oomlout/oomlout_oobb_part_holder_bearing_version_5/navigation_oobb/oobb/part/plate/bearing/6705_bearing_size/3_width/3_height/12_depth/motor_servo_standard_01_horn_adapter_screws/3dpr.png

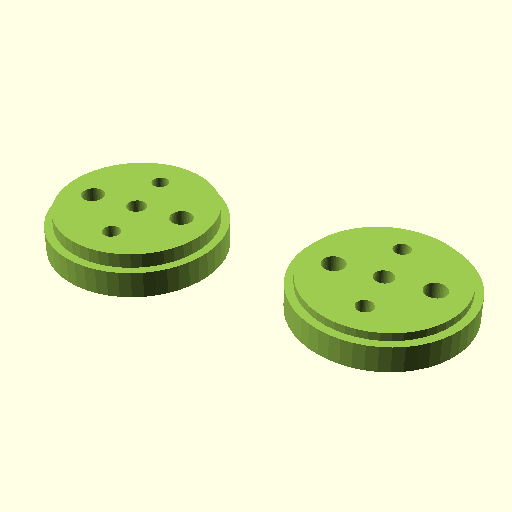
navigation_oobb/oobb/part/plate/bearing/6705_bearing_size/3_width/3_height/12_depth/motor_servo_standard_01_horn_adapter_screws/3dpr.png
