oomlout/oomlout_oobb_part_holder_bearing_version_5/navigation_oobb/oobb/part/plate/bearing/6709_bearing_size/5_width/5_height/12_depth/inside_embedded_m3_nuts/3dpr.png

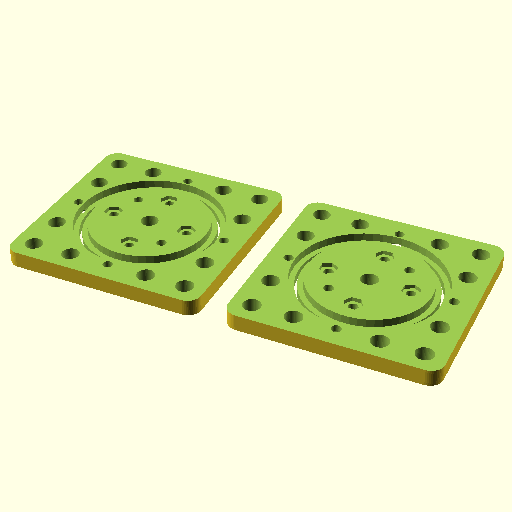
navigation_oobb/oobb/part/plate/bearing/6709_bearing_size/5_width/5_height/12_depth/inside_embedded_m3_nuts/3dpr.png
