oomlout/oomlout_oobb_part_holder_bearing_version_5/navigation_oobb/oobb/part/plate/bearing/6709_bearing_size/5_width/5_height/12_depth/motor_building_block_large_01/3dpr.stl

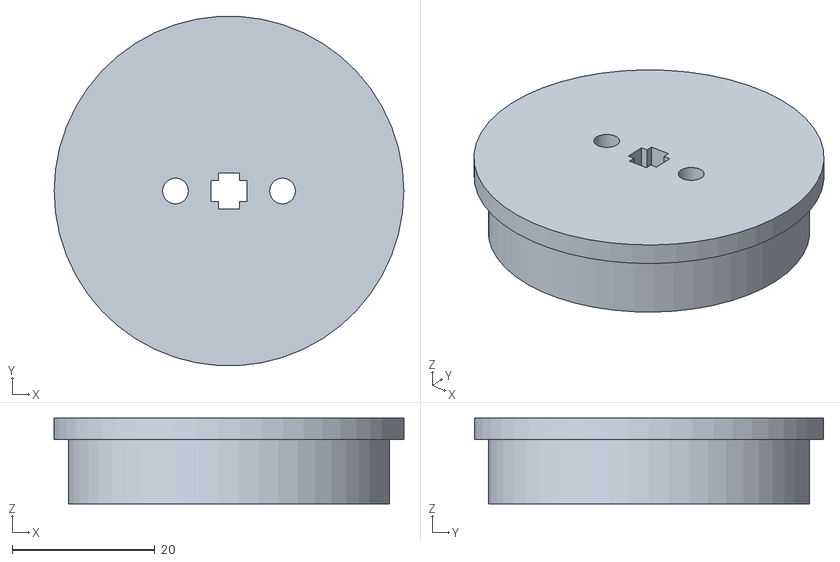
[picture p25: CAD file, 2026-10-08]
navigation_oobb/oobb/part/plate/bearing/6709_bearing_size/5_width/5_height/12_depth/motor_building_block_large_01/3dpr.stl
49.0 x 48.9 x 12.0
