oomlout/oomlout_oobb_part_holder_bearing_version_5/navigation_oobb/oobb/part/plate/bearing/6709_bearing_size/5_width/5_height/12_depth/motor_n20/3dpr.stl

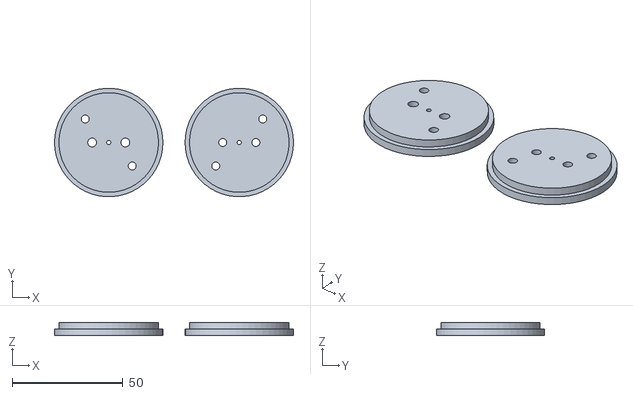
[picture p26: CAD file, 2026-10-08]
navigation_oobb/oobb/part/plate/bearing/6709_bearing_size/5_width/5_height/12_depth/motor_n20/3dpr.stl
108.0 x 48.9 x 6.00
