oomlout/oomlout_oobb_part_holder_bearing_version_5/navigation_oobb/oobb/part/plate/bearing/6709_bearing_size/5_width/5_height/12_depth/motor_servo_micro_01/true.stl

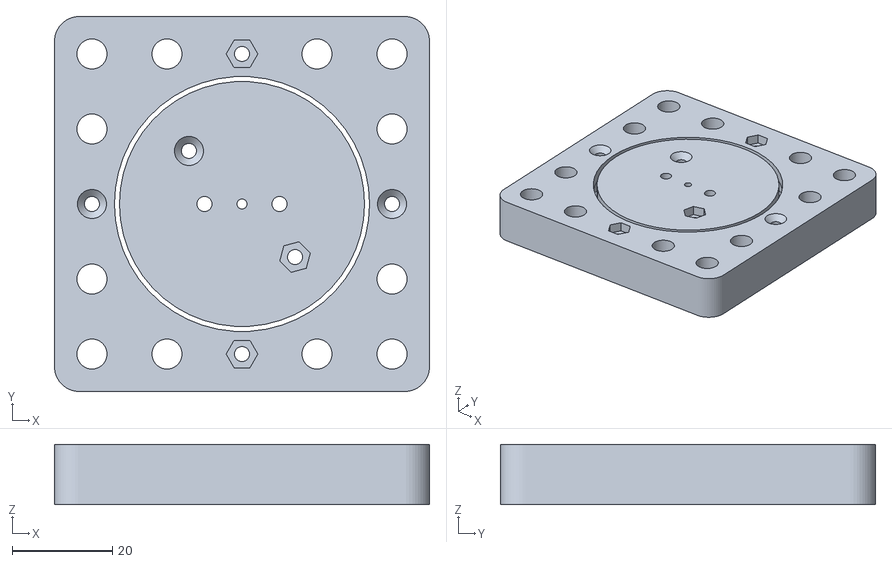
[picture p27: CAD file, 2026-10-08]
navigation_oobb/oobb/part/plate/bearing/6709_bearing_size/5_width/5_height/12_depth/motor_servo_micro_01/true.stl
75.0 x 75.0 x 12.0
