oomlout/oomlout_oobb_part_holder_bearing_version_5/navigation_oobb/oobb/part/plate/bearing/6803_bearing_size/3_width/3_height/12_depth/laser.stl

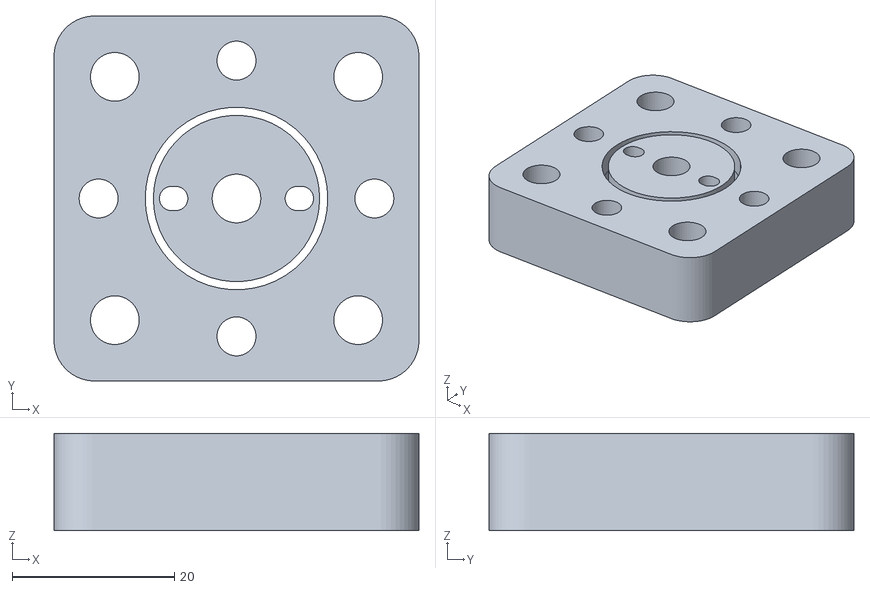
[picture p28: CAD file, 2026-10-08]
navigation_oobb/oobb/part/plate/bearing/6803_bearing_size/3_width/3_height/12_depth/laser.stl
45.0 x 45.0 x 12.0
