oomlout/oomlout_oobb_part_holder_bearing_version_5/navigation_oobb/oobb/part/plate/bearing/6810_bearing_size/7_width/5_height/12_depth/inside_embedded_m3_nuts/true.stl

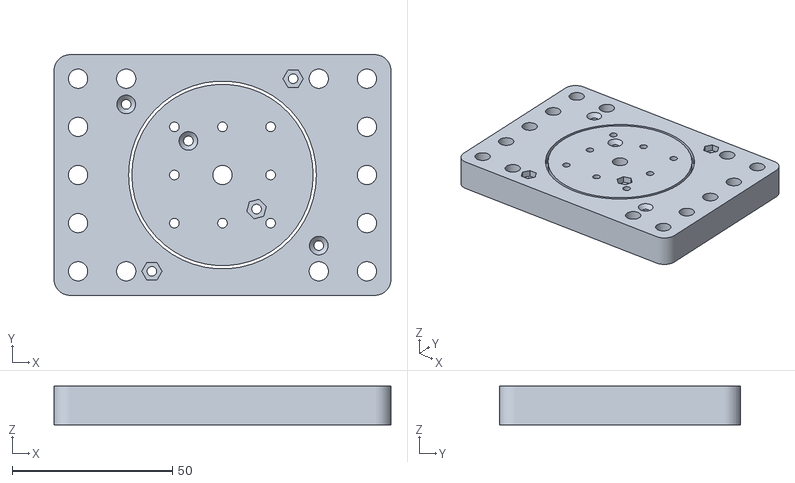
[picture p30: CAD file, 2026-10-08]
navigation_oobb/oobb/part/plate/bearing/6810_bearing_size/7_width/5_height/12_depth/inside_embedded_m3_nuts/true.stl
105.0 x 75.0 x 12.0
