oomlout/oomlout_oobb_part_holder_bearing_version_5/navigation_oobb/oobb/part/plate_90_degree/bearing/606_bearing_size/3_width/3_height/12_depth/3dpr.stl

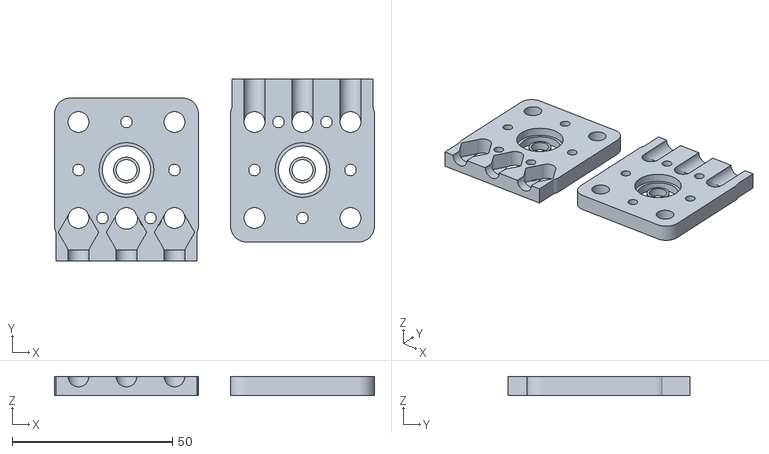
[picture p31: CAD file, 2026-10-08]
navigation_oobb/oobb/part/plate_90_degree/bearing/606_bearing_size/3_width/3_height/12_depth/3dpr.stl
100.0 x 57.0 x 6.00
