oomlout/oomlout_oobb_part_holder_bearing_version_5/navigation_oobb/oobb/part/plate_90_degree/bearing/606_bearing_size/3_width/3_height/12_depth/basic/laser.stl

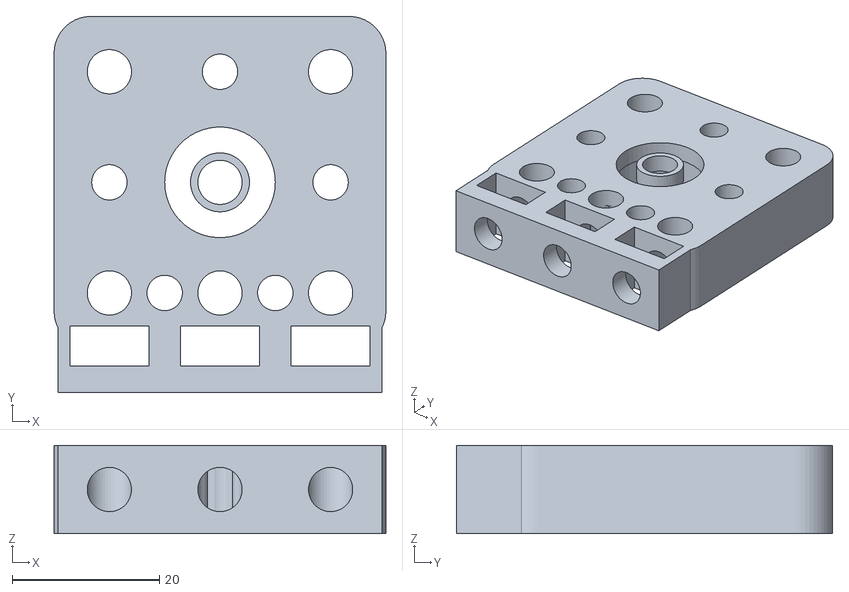
[picture p32: CAD file, 2026-10-08]
navigation_oobb/oobb/part/plate_90_degree/bearing/606_bearing_size/3_width/3_height/12_depth/basic/laser.stl
45.0 x 51.0 x 12.0
