oomlout/oomlout_oobb_part_holder_bearing_version_5/parts/oobb_part_plate_90_degree_bearing_606_bearing_size_3_width_3_height_12_depth_basic/true.stl

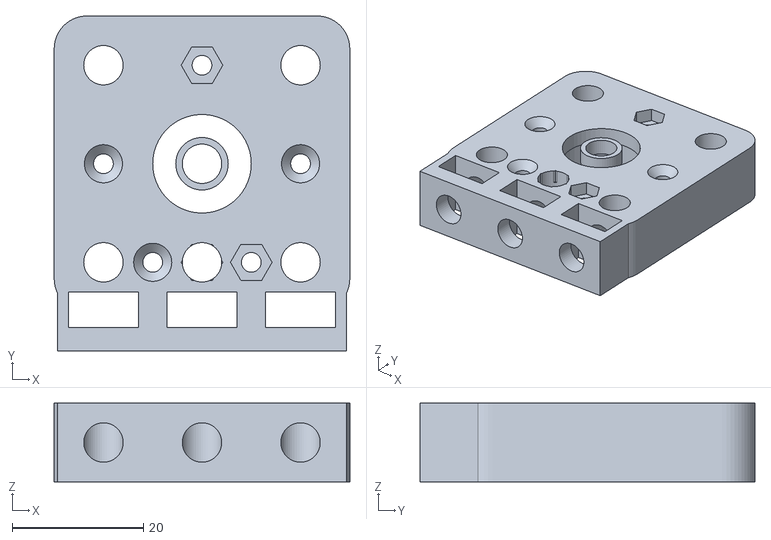
[picture p33: CAD file, 2026-10-08]
parts/oobb_part_plate_90_degree_bearing_606_bearing_size_3_width_3_height_12_depth_basic/true.stl
45.0 x 51.0 x 12.0
