oomlout/oomlout_oobb_part_holder_bearing_version_5/parts/oobb_part_plate_bearing_606_bearing_size_3_width_3_height_12_depth/3dpr.stl

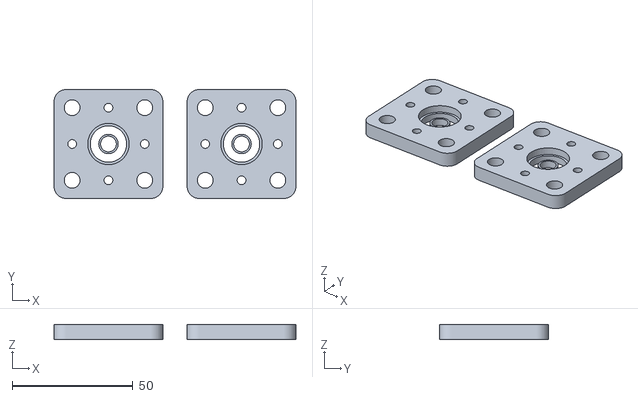
[picture p34: CAD file, 2026-10-08]
parts/oobb_part_plate_bearing_606_bearing_size_3_width_3_height_12_depth/3dpr.stl
100.0 x 45.0 x 6.00
