oomlout/oomlout_oobb_part_holder_bearing_version_5/parts/oobb_part_plate_bearing_6704_bearing_size_3_width_3_height_12_depth_motor_gearmotor_01/true.stl

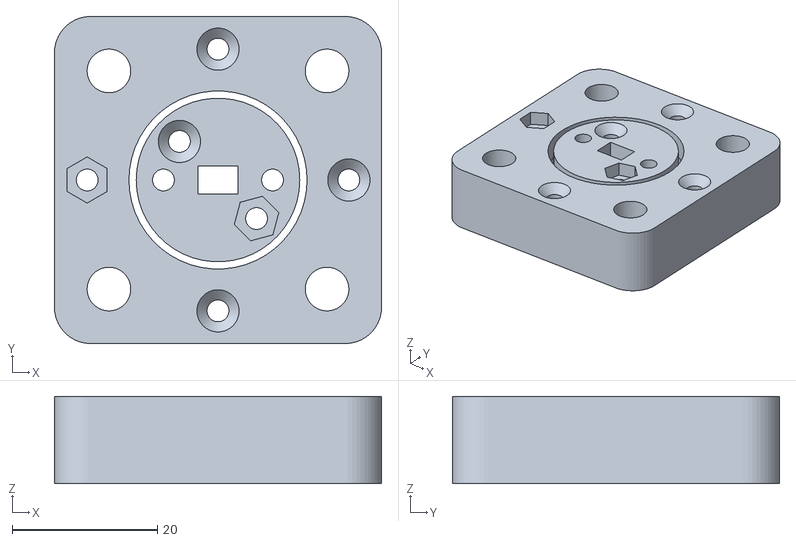
[picture p37: CAD file, 2026-10-08]
parts/oobb_part_plate_bearing_6704_bearing_size_3_width_3_height_12_depth_motor_gearmotor_01/true.stl
45.0 x 45.0 x 12.0
