oomlout/oomlout_oobb_part_holder_bearing_version_5/parts/oobb_part_plate_bearing_6704_bearing_size_3_width_3_height_12_depth_motor_n20/3dpr.stl

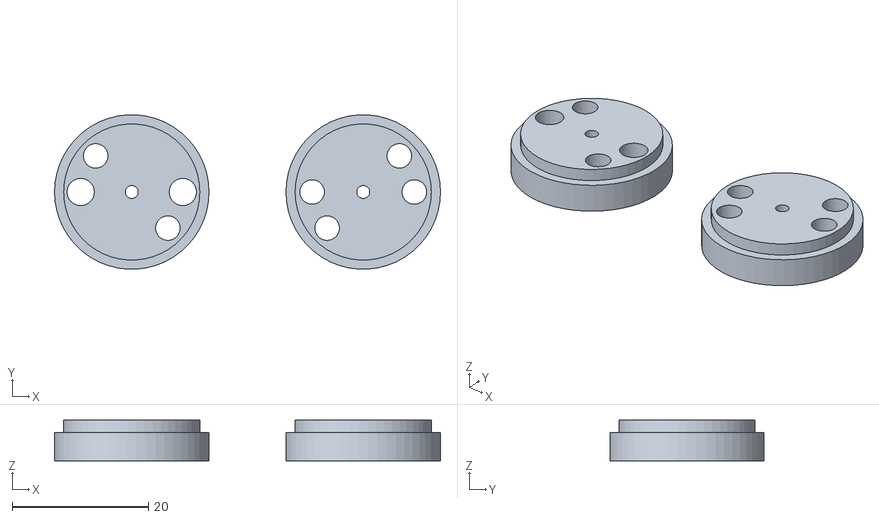
[picture p38: CAD file, 2026-10-08]
parts/oobb_part_plate_bearing_6704_bearing_size_3_width_3_height_12_depth_motor_n20/3dpr.stl
56.7 x 22.7 x 6.00
