oomlout/oomlout_oobb_part_holder_bearing_version_5/parts/oobb_part_plate_bearing_6705_bearing_size_3_width_3_height_12_depth_motor_n20/true.stl

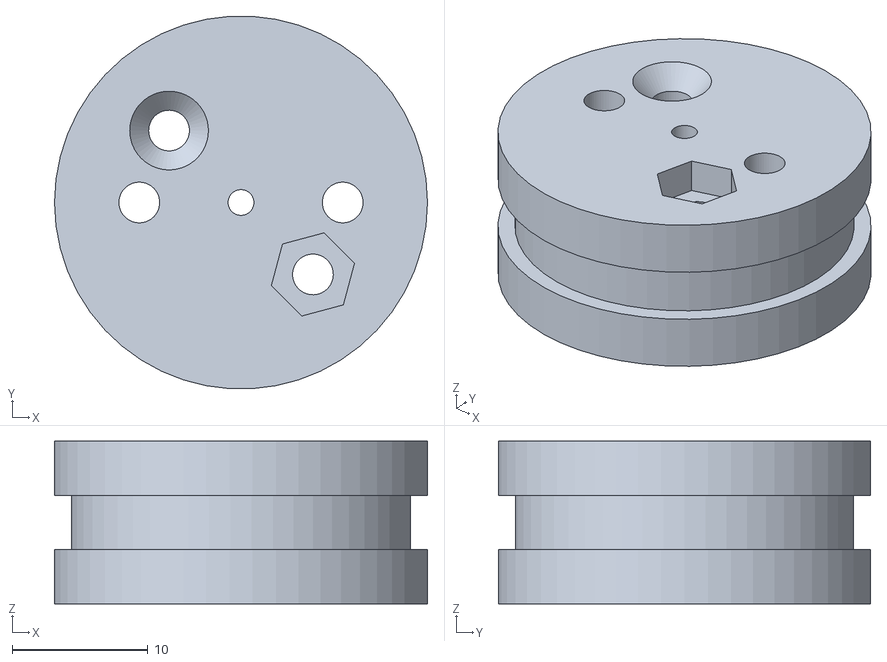
[picture p39: CAD file, 2026-10-08]
parts/oobb_part_plate_bearing_6705_bearing_size_3_width_3_height_12_depth_motor_n20/true.stl
27.5 x 27.4 x 12.0
