oomlout/oomlout_oobb_part_holder_bearing_version_5/parts/oobb_part_plate_bearing_6709_bearing_size_5_width_5_height_12_depth_inside_embedded_m6_nuts/laser.stl

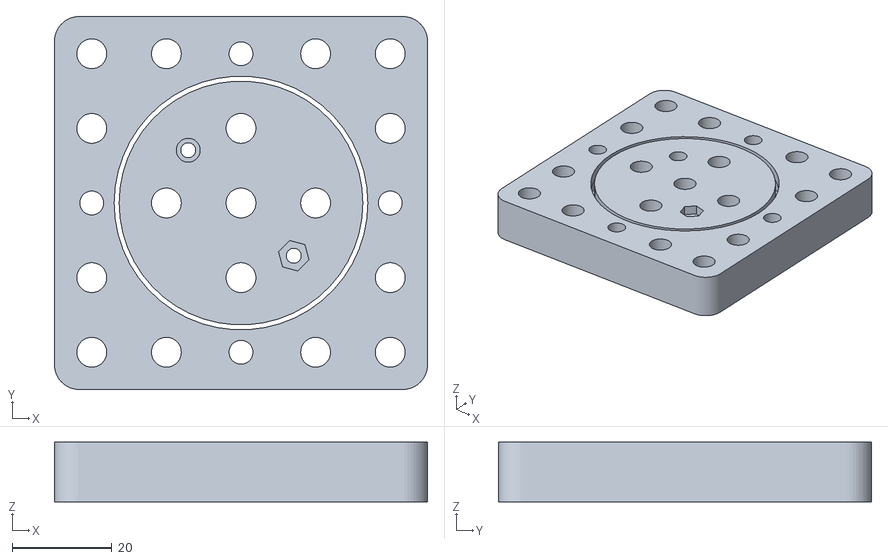
[picture p40: CAD file, 2026-10-08]
parts/oobb_part_plate_bearing_6709_bearing_size_5_width_5_height_12_depth_inside_embedded_m6_nuts/laser.stl
75.0 x 75.0 x 12.0
