oomlout/oomlout_oobb_part_holder_bearing_version_5/parts/oobb_part_plate_bearing_6709_bearing_size_5_width_5_height_12_depth_motor_building_block_large_01/laser.stl

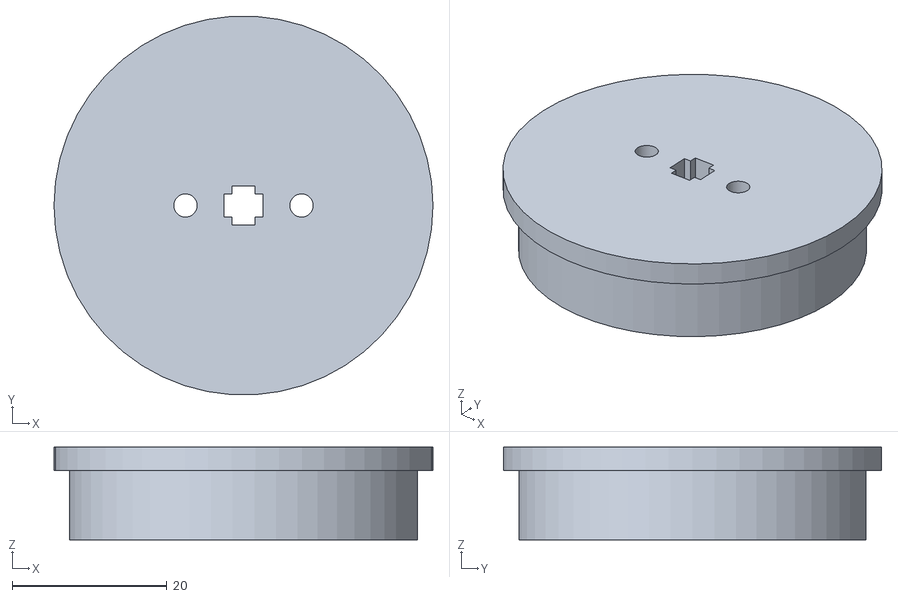
[picture p41: CAD file, 2026-10-08]
parts/oobb_part_plate_bearing_6709_bearing_size_5_width_5_height_12_depth_motor_building_block_large_01/laser.stl
49.0 x 48.9 x 12.0
