oomlout/oomlout_oobb_part_holder_bearing_version_5/parts/oobb_part_plate_bearing_6810_bearing_size_7_width_5_height_12_depth/laser.stl

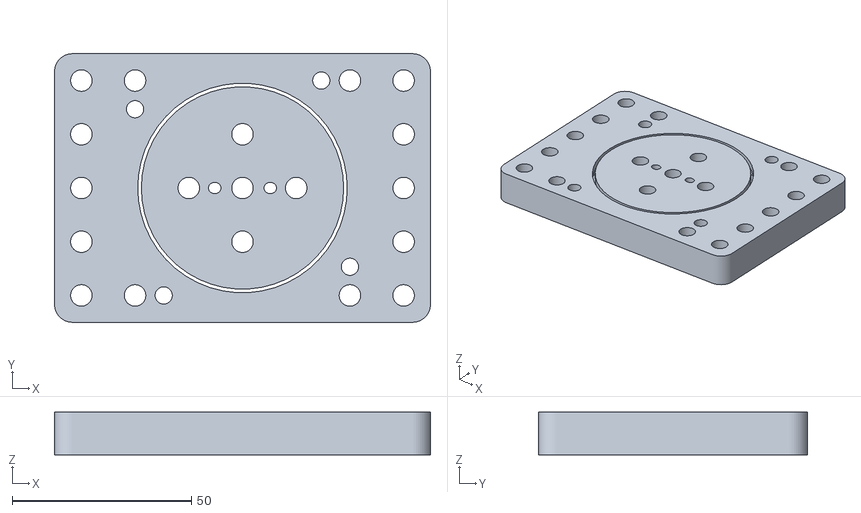
[picture p43: CAD file, 2026-10-08]
parts/oobb_part_plate_bearing_6810_bearing_size_7_width_5_height_12_depth/laser.stl
105.0 x 75.0 x 12.0
