oomlout/oomlout_oobb_part_holder_bearing_version_5/navigation_oobb/oobb/part/plate/bearing/606_bearing_size/3_width/3_height/12_depth/true.stl

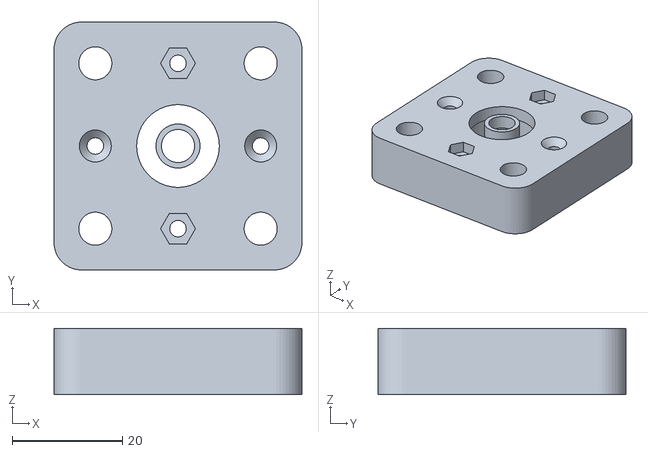
[picture p44: CAD file, 2026-10-08]
navigation_oobb/oobb/part/plate/bearing/606_bearing_size/3_width/3_height/12_depth/true.stl
45.0 x 45.0 x 12.0
