oomlout/oomlout_oobb_part_holder_bearing_version_5/navigation_oobb/oobb/part/plate/bearing/6810_bearing_size/7_width/5_height/12_depth/inside_embedded_m3_nuts/3dpr.stl

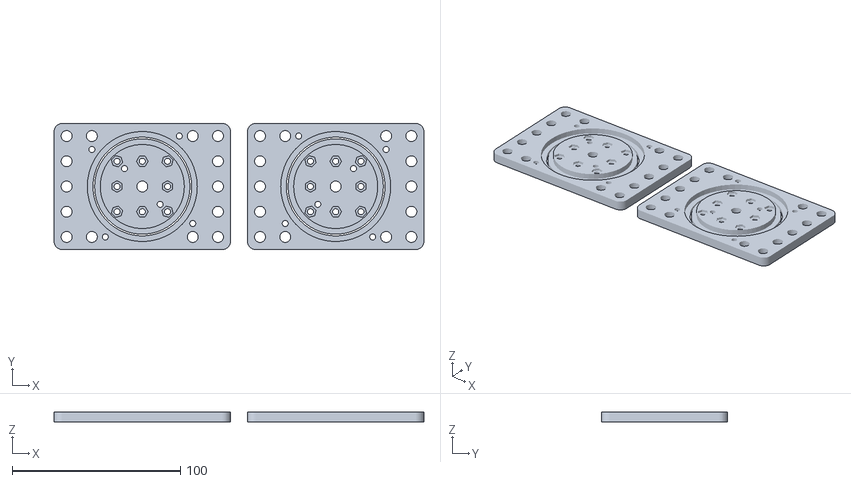
[picture p46: CAD file, 2026-10-08]
navigation_oobb/oobb/part/plate/bearing/6810_bearing_size/7_width/5_height/12_depth/inside_embedded_m3_nuts/3dpr.stl
220.0 x 75.0 x 6.00
