oomlout/oomlout_oobb_part_holder_bearing_version_5/parts/oobb_part_plate_bearing_608_bearing_size_3_width_3_height_12_depth/laser.stl

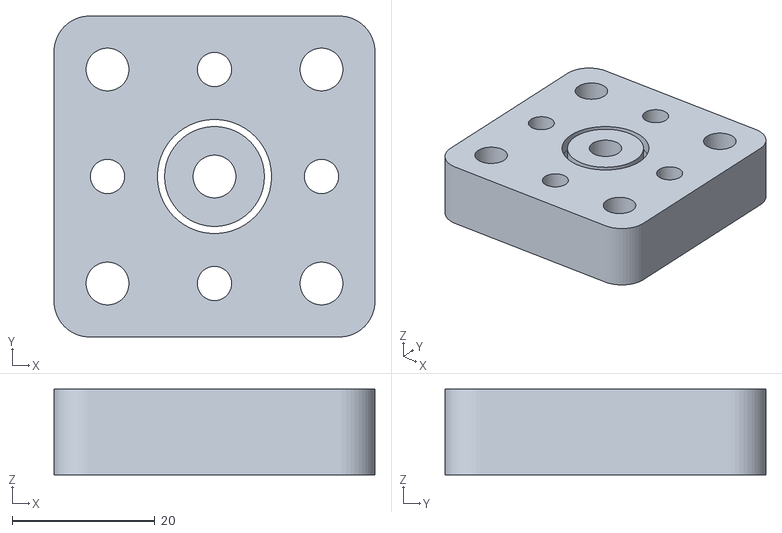
[picture p47: CAD file, 2026-10-08]
parts/oobb_part_plate_bearing_608_bearing_size_3_width_3_height_12_depth/laser.stl
45.0 x 45.0 x 12.0
