oomlout/oomlout_oobb_part_holder_bearing_version_5/parts/oobb_part_plate_bearing_6808_bearing_size_5_width_5_height_12_depth/3dpr.stl

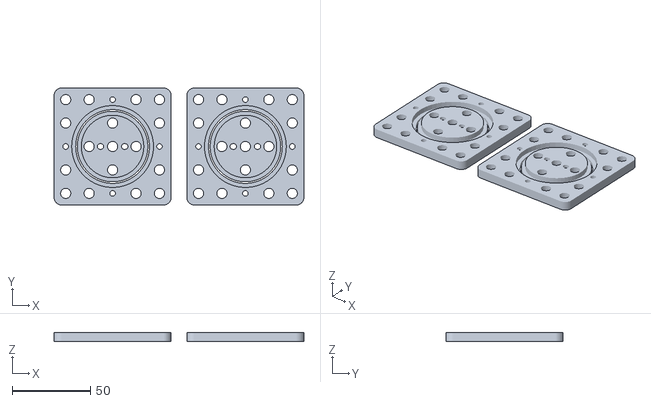
[picture p48: CAD file, 2026-10-08]
parts/oobb_part_plate_bearing_6808_bearing_size_5_width_5_height_12_depth/3dpr.stl
160.0 x 75.0 x 6.00
