oomlout/oomlout_oobb_part_holder_bearing_version_5/navigation_oobb/oobb/part/plate/bearing/6705_bearing_size/3_width/3_height/12_depth/motor_building_block_large_01/3dpr.stl

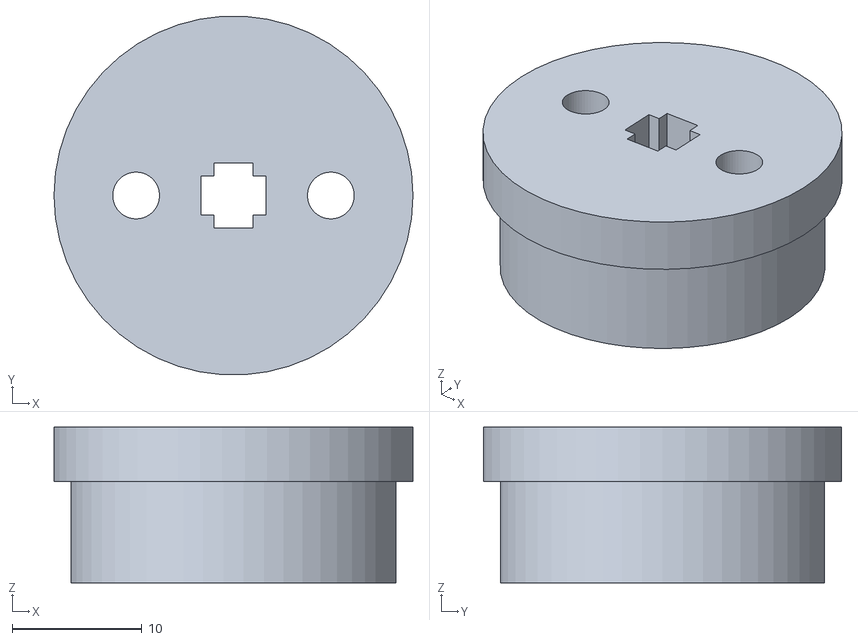
[picture p49: CAD file, 2026-10-08]
navigation_oobb/oobb/part/plate/bearing/6705_bearing_size/3_width/3_height/12_depth/motor_building_block_large_01/3dpr.stl
27.6 x 27.6 x 12.0
