oomlout/oomlout_oobb_part_holder_bearing_version_5/parts/oobb_part_plate_bearing_6704_bearing_size_3_width_3_height_12_depth_motor_gearmotor_01/3dpr.scad

$fn = 50;

difference() {
	union() {
		translate(v = [0, 0, 0]) {
			rotate(a = [0, 0, 0]) {
				difference() {
					union() {
						translate(v = [0, 0, 6.0]) {
							rotate(a = [0, 0, 0]) {
								difference() {
									union() {
										translate(v = [0, 0, -6.0]) {
											hull() {
												translate(v = [-17.5, 17.5, 0]) {
													cylinder(h = 12, r = 5);
												}
												translate(v = [17.5, 17.5, 0]) {
													cylinder(h = 12, r = 5);
												}
												translate(v = [-17.5, -17.5, 0]) {
													cylinder(h = 12, r = 5);
												}
												translate(v = [17.5, -17.5, 0]) {
													cylinder(h = 12, r = 5);
												}
											}
										}
									}
									union() {
										translate(v = [0, 0, 0]) {
											rotate(a = [0, 0, 0]) {
												difference() {
													union() {
														translate(v = [0, 0, -1.8]) {
															cylinder(h = 3.6, r = 13.7);
														}
													}
													union() {
														translate(v = [0, 0, -1.81]) {
															cylinder(h = 3.62, r = 10.0);
														}
													}
												}
											}
										}
										translate(v = [0, 0, 0]) {
											rotate(a = [0, 0, 0]) {
												difference() {
													union() {
														translate(v = [0, 0, -21.0]) {
															cylinder(h = 42, r = 12.35);
														}
													}
													union() {
														translate(v = [0, 0, -21.01]) {
															cylinder(h = 42.02, r = 11.35);
														}
													}
												}
											}
										}
										translate(v = [18.0, 0, 6.0]) {
											rotate(a = [0, 0, 0]) {
												difference() {
													union() {
														translate(v = [0, 0, -12.0]) {
															rotate(a = [0, 0, 30]) {
																difference() {
																	union() {
																		linear_extrude(height = 3) {
																			polygon(points = [[3.4619999999999997, 0.0], [1.7310000000000003, 2.9981799479017264], [-1.7309999999999992, 2.9981799479017264], [-3.4619999999999997, 4.2397272186481365e-16], [-1.7310000000000014, -2.998179947901726], [1.7309999999999977, -2.9981799479017277]]);
																		}
																		translate(v = [-1.75, -3.25, -0.3]) {
																			cube(size = [3.5, 6.5, 0.3]);
																		}
																		translate(v = [-1.75, -1.75, -0.6]) {
																			cube(size = [3.5, 3.5, 0.3]);
																		}
																		translate(v = [-1.75, -3.25, 3]) {
																			cube(size = [3.5, 6.5, 0.3]);
																		}
																		translate(v = [-1.75, -1.75, 3.3]) {
																			cube(size = [3.5, 3.5, 0.3]);
																		}
																		translate(v = [0, 0, -100.0]) {
																			cylinder(h = 200, r = 1.8);
																		}
																	}
																	union();
																}
															}
														}
														translate(v = [0, 0, -1.9]) {
															cylinder(h = 1.9, r1 = 1.8, r2 = 3.6);
														}
														translate(v = [0, 0, -12.0]) {
															cylinder(h = 12, r = 1.8);
														}
													}
													union();
												}
											}
										}
										translate(v = [0, -18.0, 6.0]) {
											rotate(a = [0, 0, 0]) {
												difference() {
													union() {
														translate(v = [0, 0, -12.0]) {
															rotate(a = [0, 0, 0]) {
																difference() {
																	union() {
																		linear_extrude(height = 3) {
																			polygon(points = [[3.4619999999999997, 0.0], [1.7310000000000003, 2.9981799479017264], [-1.7309999999999992, 2.9981799479017264], [-3.4619999999999997, 4.2397272186481365e-16], [-1.7310000000000014, -2.998179947901726], [1.7309999999999977, -2.9981799479017277]]);
																		}
																		translate(v = [-1.75, -3.25, -0.3]) {
																			cube(size = [3.5, 6.5, 0.3]);
																		}
																		translate(v = [-1.75, -1.75, -0.6]) {
																			cube(size = [3.5, 3.5, 0.3]);
																		}
																		translate(v = [-1.75, -3.25, 3]) {
																			cube(size = [3.5, 6.5, 0.3]);
																		}
																		translate(v = [-1.75, -1.75, 3.3]) {
																			cube(size = [3.5, 3.5, 0.3]);
																		}
																		translate(v = [0, 0, -100.0]) {
																			cylinder(h = 200, r = 1.8);
																		}
																	}
																	union();
																}
															}
														}
														translate(v = [0, 0, -1.9]) {
															cylinder(h = 1.9, r1 = 1.8, r2 = 3.6);
														}
														translate(v = [0, 0, -12.0]) {
															cylinder(h = 12, r = 1.8);
														}
													}
													union();
												}
											}
										}
										translate(v = [-18.0, 0, -6.0]) {
											rotate(a = [0, 180, 0]) {
												difference() {
													union() {
														translate(v = [0, 0, -12.0]) {
															rotate(a = [0, 0, 30]) {
																difference() {
																	union() {
																		linear_extrude(height = 3) {
																			polygon(points = [[3.4619999999999997, 0.0], [1.7310000000000003, 2.9981799479017264], [-1.7309999999999992, 2.9981799479017264], [-3.4619999999999997, 4.2397272186481365e-16], [-1.7310000000000014, -2.998179947901726], [1.7309999999999977, -2.9981799479017277]]);
																		}
																		translate(v = [-1.75, -3.25, -0.3]) {
																			cube(size = [3.5, 6.5, 0.3]);
																		}
																		translate(v = [-1.75, -1.75, -0.6]) {
																			cube(size = [3.5, 3.5, 0.3]);
																		}
																		translate(v = [-1.75, -3.25, 3]) {
																			cube(size = [3.5, 6.5, 0.3]);
																		}
																		translate(v = [-1.75, -1.75, 3.3]) {
																			cube(size = [3.5, 3.5, 0.3]);
																		}
																		translate(v = [0, 0, -100.0]) {
																			cylinder(h = 200, r = 1.8);
																		}
																	}
																	union();
																}
															}
														}
														translate(v = [0, 0, -1.9]) {
															cylinder(h = 1.9, r1 = 1.8, r2 = 3.6);
														}
														translate(v = [0, 0, -12.0]) {
															cylinder(h = 12, r = 1.8);
														}
													}
													union();
												}
											}
										}
										translate(v = [0, 18.0, 6.0]) {
											rotate(a = [0, 0, 0]) {
												difference() {
													union() {
														translate(v = [0, 0, -12.0]) {
															rotate(a = [0, 0, 0]) {
																difference() {
																	union() {
																		linear_extrude(height = 3) {
																			polygon(points = [[3.4619999999999997, 0.0], [1.7310000000000003, 2.9981799479017264], [-1.7309999999999992, 2.9981799479017264], [-3.4619999999999997, 4.2397272186481365e-16], [-1.7310000000000014, -2.998179947901726], [1.7309999999999977, -2.9981799479017277]]);
																		}
																		translate(v = [-1.75, -3.25, -0.3]) {
																			cube(size = [3.5, 6.5, 0.3]);
																		}
																		translate(v = [-1.75, -1.75, -0.6]) {
																			cube(size = [3.5, 3.5, 0.3]);
																		}
																		translate(v = [-1.75, -3.25, 3]) {
																			cube(size = [3.5, 6.5, 0.3]);
																		}
																		translate(v = [-1.75, -1.75, 3.3]) {
																			cube(size = [3.5, 3.5, 0.3]);
																		}
																		translate(v = [0, 0, -100.0]) {
																			cylinder(h = 200, r = 1.8);
																		}
																	}
																	union();
																}
															}
														}
														translate(v = [0, 0, -1.9]) {
															cylinder(h = 1.9, r1 = 1.8, r2 = 3.6);
														}
														translate(v = [0, 0, -12.0]) {
															cylinder(h = 12, r = 1.8);
														}
													}
													union();
												}
											}
										}
										translate(v = [-5.303300858899107, 5.303300858899107, 6.0]) {
											rotate(a = [0, 0, 0]) {
												difference() {
													union() {
														translate(v = [0, 0, -12.0]) {
															rotate(a = [0, 0, 45.0]) {
																difference() {
																	union() {
																		linear_extrude(height = 3) {
																			polygon(points = [[3.4619999999999997, 0.0], [1.7310000000000003, 2.9981799479017264], [-1.7309999999999992, 2.9981799479017264], [-3.4619999999999997, 4.2397272186481365e-16], [-1.7310000000000014, -2.998179947901726], [1.7309999999999977, -2.9981799479017277]]);
																		}
																		translate(v = [-1.75, -3.25, -0.3]) {
																			cube(size = [3.5, 6.5, 0.3]);
																		}
																		translate(v = [-1.75, -1.75, -0.6]) {
																			cube(size = [3.5, 3.5, 0.3]);
																		}
																		translate(v = [-1.75, -3.25, 3]) {
																			cube(size = [3.5, 6.5, 0.3]);
																		}
																		translate(v = [-1.75, -1.75, 3.3]) {
																			cube(size = [3.5, 3.5, 0.3]);
																		}
																		translate(v = [0, 0, -100.0]) {
																			cylinder(h = 200, r = 1.8);
																		}
																	}
																	union();
																}
															}
														}
														translate(v = [0, 0, -1.9]) {
															cylinder(h = 1.9, r1 = 1.8, r2 = 3.6);
														}
														translate(v = [0, 0, -12.0]) {
															cylinder(h = 12, r = 1.8);
														}
													}
													union();
												}
											}
										}
										translate(v = [5.303300858899107, -5.303300858899107, -6.0]) {
											rotate(a = [0, 180, 0]) {
												difference() {
													union() {
														translate(v = [0, 0, -12.0]) {
															rotate(a = [0, 0, 45.0]) {
																difference() {
																	union() {
																		linear_extrude(height = 3) {
																			polygon(points = [[3.4619999999999997, 0.0], [1.7310000000000003, 2.9981799479017264], [-1.7309999999999992, 2.9981799479017264], [-3.4619999999999997, 4.2397272186481365e-16], [-1.7310000000000014, -2.998179947901726], [1.7309999999999977, -2.9981799479017277]]);
																		}
																		translate(v = [-1.75, -3.25, -0.3]) {
																			cube(size = [3.5, 6.5, 0.3]);
																		}
																		translate(v = [-1.75, -1.75, -0.6]) {
																			cube(size = [3.5, 3.5, 0.3]);
																		}
																		translate(v = [-1.75, -3.25, 3]) {
																			cube(size = [3.5, 6.5, 0.3]);
																		}
																		translate(v = [-1.75, -1.75, 3.3]) {
																			cube(size = [3.5, 3.5, 0.3]);
																		}
																		translate(v = [0, 0, -100.0]) {
																			cylinder(h = 200, r = 1.8);
																		}
																	}
																	union();
																}
															}
														}
														translate(v = [0, 0, -1.9]) {
															cylinder(h = 1.9, r1 = 1.8, r2 = 3.6);
														}
														translate(v = [0, 0, -12.0]) {
															cylinder(h = 12, r = 1.8);
														}
													}
													union();
												}
											}
										}
										translate(v = [5.303300858899107, 5.303300858899107, 6.0]) {
											rotate(a = [0, 0, 0]) {
												difference() {
													union() {
														translate(v = [0, 0, -12.0]) {
															rotate(a = [0, 0, 45.0]) {
																difference() {
																	union() {
																		linear_extrude(height = 3) {
																			polygon(points = [[3.4619999999999997, 0.0], [1.7310000000000003, 2.9981799479017264], [-1.7309999999999992, 2.9981799479017264], [-3.4619999999999997, 4.2397272186481365e-16], [-1.7310000000000014, -2.998179947901726], [1.7309999999999977, -2.9981799479017277]]);
																		}
																		translate(v = [-1.75, -3.25, -0.3]) {
																			cube(size = [3.5, 6.5, 0.3]);
																		}
																		translate(v = [-1.75, -1.75, -0.6]) {
																			cube(size = [3.5, 3.5, 0.3]);
																		}
																		translate(v = [-1.75, -3.25, 3]) {
																			cube(size = [3.5, 6.5, 0.3]);
																		}
																		translate(v = [-1.75, -1.75, 3.3]) {
																			cube(size = [3.5, 3.5, 0.3]);
																		}
																		translate(v = [0, 0, -100.0]) {
																			cylinder(h = 200, r = 1.8);
																		}
																	}
																	union();
																}
															}
														}
														translate(v = [0, 0, -1.9]) {
															cylinder(h = 1.9, r1 = 1.8, r2 = 3.6);
														}
														translate(v = [0, 0, -12.0]) {
															cylinder(h = 12, r = 1.8);
														}
													}
													union();
												}
											}
										}
										translate(v = [-5.303300858899107, -5.303300858899107, 6.0]) {
											rotate(a = [0, 0, 0]) {
												difference() {
													union() {
														translate(v = [0, 0, -12.0]) {
															rotate(a = [0, 0, 45.0]) {
																difference() {
																	union() {
																		linear_extrude(height = 3) {
																			polygon(points = [[3.4619999999999997, 0.0], [1.7310000000000003, 2.9981799479017264], [-1.7309999999999992, 2.9981799479017264], [-3.4619999999999997, 4.2397272186481365e-16], [-1.7310000000000014, -2.998179947901726], [1.7309999999999977, -2.9981799479017277]]);
																		}
																		translate(v = [-1.75, -3.25, -0.3]) {
																			cube(size = [3.5, 6.5, 0.3]);
																		}
																		translate(v = [-1.75, -1.75, -0.6]) {
																			cube(size = [3.5, 3.5, 0.3]);
																		}
																		translate(v = [-1.75, -3.25, 3]) {
																			cube(size = [3.5, 6.5, 0.3]);
																		}
																		translate(v = [-1.75, -1.75, 3.3]) {
																			cube(size = [3.5, 3.5, 0.3]);
																		}
																		translate(v = [0, 0, -100.0]) {
																			cylinder(h = 200, r = 1.8);
																		}
																	}
																	union();
																}
															}
														}
														translate(v = [0, 0, -1.9]) {
															cylinder(h = 1.9, r1 = 1.8, r2 = 3.6);
														}
														translate(v = [0, 0, -12.0]) {
															cylinder(h = 12, r = 1.8);
														}
													}
													union();
												}
											}
										}
										translate(v = [-15.0, -15.0, -100.0]) {
											cylinder(h = 200, r = 3.25);
										}
										translate(v = [-15.0, 15.0, -100.0]) {
											cylinder(h = 200, r = 3.25);
										}
										translate(v = [15.0, -15.0, -100.0]) {
											cylinder(h = 200, r = 3.25);
										}
										translate(v = [15.0, 15.0, -100.0]) {
											cylinder(h = 200, r = 3.25);
										}
										translate(v = [-7.5, 0, -6.0]) {
											cylinder(h = 6, r = 2.0);
										}
										translate(v = [-7.5, 0, -7.0]) {
											cylinder(h = 14, r = 1.8);
										}
										translate(v = [7.5, 0, -6.0]) {
											cylinder(h = 6, r = 2.0);
										}
										translate(v = [7.5, 0, -7.0]) {
											cylinder(h = 14, r = 1.8);
										}
										translate(v = [-2.75, -1.925, -7.0]) {
											cube(size = [5.5, 3.85, 14]);
										}
										translate(v = [-250, -250, 0]) {
											cube(size = [500, 500, 500]);
										}
									}
								}
							}
						}
						translate(v = [55, 0, 6.0]) {
							rotate(a = [180, 0, 0]) {
								difference() {
									union() {
										translate(v = [0, 0, -6.0]) {
											hull() {
												translate(v = [-17.5, 17.5, 0]) {
													cylinder(h = 12, r = 5);
												}
												translate(v = [17.5, 17.5, 0]) {
													cylinder(h = 12, r = 5);
												}
												translate(v = [-17.5, -17.5, 0]) {
													cylinder(h = 12, r = 5);
												}
												translate(v = [17.5, -17.5, 0]) {
													cylinder(h = 12, r = 5);
												}
											}
										}
									}
									union() {
										translate(v = [0, 0, 0]) {
											rotate(a = [0, 0, 0]) {
												difference() {
													union() {
														translate(v = [0, 0, -1.8]) {
															cylinder(h = 3.6, r = 13.7);
														}
													}
													union() {
														translate(v = [0, 0, -1.81]) {
															cylinder(h = 3.62, r = 10.0);
														}
													}
												}
											}
										}
										translate(v = [0, 0, 0]) {
											rotate(a = [0, 0, 0]) {
												difference() {
													union() {
														translate(v = [0, 0, -21.0]) {
															cylinder(h = 42, r = 12.35);
														}
													}
													union() {
														translate(v = [0, 0, -21.01]) {
															cylinder(h = 42.02, r = 11.35);
														}
													}
												}
											}
										}
										translate(v = [18.0, 0, 6.0]) {
											rotate(a = [0, 0, 0]) {
												difference() {
													union() {
														translate(v = [0, 0, -12.0]) {
															rotate(a = [0, 0, 30]) {
																difference() {
																	union() {
																		linear_extrude(height = 3) {
																			polygon(points = [[3.4619999999999997, 0.0], [1.7310000000000003, 2.9981799479017264], [-1.7309999999999992, 2.9981799479017264], [-3.4619999999999997, 4.2397272186481365e-16], [-1.7310000000000014, -2.998179947901726], [1.7309999999999977, -2.9981799479017277]]);
																		}
																		translate(v = [-1.75, -3.25, -0.3]) {
																			cube(size = [3.5, 6.5, 0.3]);
																		}
																		translate(v = [-1.75, -1.75, -0.6]) {
																			cube(size = [3.5, 3.5, 0.3]);
																		}
																		translate(v = [-1.75, -3.25, 3]) {
																			cube(size = [3.5, 6.5, 0.3]);
																		}
																		translate(v = [-1.75, -1.75, 3.3]) {
																			cube(size = [3.5, 3.5, 0.3]);
																		}
																		translate(v = [0, 0, -100.0]) {
																			cylinder(h = 200, r = 1.8);
																		}
																	}
																	union();
																}
															}
														}
														translate(v = [0, 0, -1.9]) {
															cylinder(h = 1.9, r1 = 1.8, r2 = 3.6);
														}
														translate(v = [0, 0, -12.0]) {
															cylinder(h = 12, r = 1.8);
														}
													}
													union();
												}
											}
										}
										translate(v = [0, -18.0, 6.0]) {
											rotate(a = [0, 0, 0]) {
												difference() {
													union() {
														translate(v = [0, 0, -12.0]) {
															rotate(a = [0, 0, 0]) {
																difference() {
																	union() {
																		linear_extrude(height = 3) {
																			polygon(points = [[3.4619999999999997, 0.0], [1.7310000000000003, 2.9981799479017264], [-1.7309999999999992, 2.9981799479017264], [-3.4619999999999997, 4.2397272186481365e-16], [-1.7310000000000014, -2.998179947901726], [1.7309999999999977, -2.9981799479017277]]);
																		}
																		translate(v = [-1.75, -3.25, -0.3]) {
																			cube(size = [3.5, 6.5, 0.3]);
																		}
																		translate(v = [-1.75, -1.75, -0.6]) {
																			cube(size = [3.5, 3.5, 0.3]);
																		}
																		translate(v = [-1.75, -3.25, 3]) {
																			cube(size = [3.5, 6.5, 0.3]);
																		}
																		translate(v = [-1.75, -1.75, 3.3]) {
																			cube(size = [3.5, 3.5, 0.3]);
																		}
																		translate(v = [0, 0, -100.0]) {
																			cylinder(h = 200, r = 1.8);
																		}
																	}
																	union();
																}
															}
														}
														translate(v = [0, 0, -1.9]) {
															cylinder(h = 1.9, r1 = 1.8, r2 = 3.6);
														}
														translate(v = [0, 0, -12.0]) {
															cylinder(h = 12, r = 1.8);
														}
													}
													union();
												}
											}
										}
										translate(v = [-18.0, 0, -6.0]) {
											rotate(a = [0, 180, 0]) {
												difference() {
													union() {
														translate(v = [0, 0, -12.0]) {
															rotate(a = [0, 0, 30]) {
																difference() {
																	union() {
																		linear_extrude(height = 3) {
																			polygon(points = [[3.4619999999999997, 0.0], [1.7310000000000003, 2.9981799479017264], [-1.7309999999999992, 2.9981799479017264], [-3.4619999999999997, 4.2397272186481365e-16], [-1.7310000000000014, -2.998179947901726], [1.7309999999999977, -2.9981799479017277]]);
																		}
																		translate(v = [-1.75, -3.25, -0.3]) {
																			cube(size = [3.5, 6.5, 0.3]);
																		}
																		translate(v = [-1.75, -1.75, -0.6]) {
																			cube(size = [3.5, 3.5, 0.3]);
																		}
																		translate(v = [-1.75, -3.25, 3]) {
																			cube(size = [3.5, 6.5, 0.3]);
																		}
																		translate(v = [-1.75, -1.75, 3.3]) {
																			cube(size = [3.5, 3.5, 0.3]);
																		}
																		translate(v = [0, 0, -100.0]) {
																			cylinder(h = 200, r = 1.8);
																		}
																	}
																	union();
																}
															}
														}
														translate(v = [0, 0, -1.9]) {
															cylinder(h = 1.9, r1 = 1.8, r2 = 3.6);
														}
														translate(v = [0, 0, -12.0]) {
															cylinder(h = 12, r = 1.8);
														}
													}
													union();
												}
											}
										}
										translate(v = [0, 18.0, 6.0]) {
											rotate(a = [0, 0, 0]) {
												difference() {
													union() {
														translate(v = [0, 0, -12.0]) {
															rotate(a = [0, 0, 0]) {
																difference() {
																	union() {
																		linear_extrude(height = 3) {
																			polygon(points = [[3.4619999999999997, 0.0], [1.7310000000000003, 2.9981799479017264], [-1.7309999999999992, 2.9981799479017264], [-3.4619999999999997, 4.2397272186481365e-16], [-1.7310000000000014, -2.998179947901726], [1.7309999999999977, -2.9981799479017277]]);
																		}
																		translate(v = [-1.75, -3.25, -0.3]) {
																			cube(size = [3.5, 6.5, 0.3]);
																		}
																		translate(v = [-1.75, -1.75, -0.6]) {
																			cube(size = [3.5, 3.5, 0.3]);
																		}
																		translate(v = [-1.75, -3.25, 3]) {
																			cube(size = [3.5, 6.5, 0.3]);
																		}
																		translate(v = [-1.75, -1.75, 3.3]) {
																			cube(size = [3.5, 3.5, 0.3]);
																		}
																		translate(v = [0, 0, -100.0]) {
																			cylinder(h = 200, r = 1.8);
																		}
																	}
																	union();
																}
															}
														}
														translate(v = [0, 0, -1.9]) {
															cylinder(h = 1.9, r1 = 1.8, r2 = 3.6);
														}
														translate(v = [0, 0, -12.0]) {
															cylinder(h = 12, r = 1.8);
														}
													}
													union();
												}
											}
										}
										translate(v = [-5.303300858899107, 5.303300858899107, 6.0]) {
											rotate(a = [0, 0, 0]) {
												difference() {
													union() {
														translate(v = [0, 0, -12.0]) {
															rotate(a = [0, 0, 45.0]) {
																difference() {
																	union() {
																		linear_extrude(height = 3) {
																			polygon(points = [[3.4619999999999997, 0.0], [1.7310000000000003, 2.9981799479017264], [-1.7309999999999992, 2.9981799479017264], [-3.4619999999999997, 4.2397272186481365e-16], [-1.7310000000000014, -2.998179947901726], [1.7309999999999977, -2.9981799479017277]]);
																		}
																		translate(v = [-1.75, -3.25, -0.3]) {
																			cube(size = [3.5, 6.5, 0.3]);
																		}
																		translate(v = [-1.75, -1.75, -0.6]) {
																			cube(size = [3.5, 3.5, 0.3]);
																		}
																		translate(v = [-1.75, -3.25, 3]) {
																			cube(size = [3.5, 6.5, 0.3]);
																		}
																		translate(v = [-1.75, -1.75, 3.3]) {
																			cube(size = [3.5, 3.5, 0.3]);
																		}
																		translate(v = [0, 0, -100.0]) {
																			cylinder(h = 200, r = 1.8);
																		}
																	}
																	union();
																}
															}
														}
														translate(v = [0, 0, -1.9]) {
															cylinder(h = 1.9, r1 = 1.8, r2 = 3.6);
														}
														translate(v = [0, 0, -12.0]) {
															cylinder(h = 12, r = 1.8);
														}
													}
													union();
												}
											}
										}
										translate(v = [5.303300858899107, -5.303300858899107, -6.0]) {
											rotate(a = [0, 180, 0]) {
												difference() {
													union() {
														translate(v = [0, 0, -12.0]) {
															rotate(a = [0, 0, 45.0]) {
																difference() {
																	union() {
																		linear_extrude(height = 3) {
																			polygon(points = [[3.4619999999999997, 0.0], [1.7310000000000003, 2.9981799479017264], [-1.7309999999999992, 2.9981799479017264], [-3.4619999999999997, 4.2397272186481365e-16], [-1.7310000000000014, -2.998179947901726], [1.7309999999999977, -2.9981799479017277]]);
																		}
																		translate(v = [-1.75, -3.25, -0.3]) {
																			cube(size = [3.5, 6.5, 0.3]);
																		}
																		translate(v = [-1.75, -1.75, -0.6]) {
																			cube(size = [3.5, 3.5, 0.3]);
																		}
																		translate(v = [-1.75, -3.25, 3]) {
																			cube(size = [3.5, 6.5, 0.3]);
																		}
																		translate(v = [-1.75, -1.75, 3.3]) {
																			cube(size = [3.5, 3.5, 0.3]);
																		}
																		translate(v = [0, 0, -100.0]) {
																			cylinder(h = 200, r = 1.8);
																		}
																	}
																	union();
																}
															}
														}
														translate(v = [0, 0, -1.9]) {
															cylinder(h = 1.9, r1 = 1.8, r2 = 3.6);
														}
														translate(v = [0, 0, -12.0]) {
															cylinder(h = 12, r = 1.8);
														}
													}
													union();
												}
											}
										}
										translate(v = [5.303300858899107, 5.303300858899107, 6.0]) {
											rotate(a = [0, 0, 0]) {
												difference() {
													union() {
														translate(v = [0, 0, -12.0]) {
															rotate(a = [0, 0, 45.0]) {
																difference() {
																	union() {
																		linear_extrude(height = 3) {
																			polygon(points = [[3.4619999999999997, 0.0], [1.7310000000000003, 2.9981799479017264], [-1.7309999999999992, 2.9981799479017264], [-3.4619999999999997, 4.2397272186481365e-16], [-1.7310000000000014, -2.998179947901726], [1.7309999999999977, -2.9981799479017277]]);
																		}
																		translate(v = [-1.75, -3.25, -0.3]) {
																			cube(size = [3.5, 6.5, 0.3]);
																		}
																		translate(v = [-1.75, -1.75, -0.6]) {
																			cube(size = [3.5, 3.5, 0.3]);
																		}
																		translate(v = [-1.75, -3.25, 3]) {
																			cube(size = [3.5, 6.5, 0.3]);
																		}
																		translate(v = [-1.75, -1.75, 3.3]) {
																			cube(size = [3.5, 3.5, 0.3]);
																		}
																		translate(v = [0, 0, -100.0]) {
																			cylinder(h = 200, r = 1.8);
																		}
																	}
																	union();
																}
															}
														}
														translate(v = [0, 0, -1.9]) {
															cylinder(h = 1.9, r1 = 1.8, r2 = 3.6);
														}
														translate(v = [0, 0, -12.0]) {
															cylinder(h = 12, r = 1.8);
														}
													}
													union();
												}
											}
										}
										translate(v = [-5.303300858899107, -5.303300858899107, 6.0]) {
											rotate(a = [0, 0, 0]) {
												difference() {
													union() {
														translate(v = [0, 0, -12.0]) {
															rotate(a = [0, 0, 45.0]) {
																difference() {
																	union() {
																		linear_extrude(height = 3) {
																			polygon(points = [[3.4619999999999997, 0.0], [1.7310000000000003, 2.9981799479017264], [-1.7309999999999992, 2.9981799479017264], [-3.4619999999999997, 4.2397272186481365e-16], [-1.7310000000000014, -2.998179947901726], [1.7309999999999977, -2.9981799479017277]]);
																		}
																		translate(v = [-1.75, -3.25, -0.3]) {
																			cube(size = [3.5, 6.5, 0.3]);
																		}
																		translate(v = [-1.75, -1.75, -0.6]) {
																			cube(size = [3.5, 3.5, 0.3]);
																		}
																		translate(v = [-1.75, -3.25, 3]) {
																			cube(size = [3.5, 6.5, 0.3]);
																		}
																		translate(v = [-1.75, -1.75, 3.3]) {
																			cube(size = [3.5, 3.5, 0.3]);
																		}
																		translate(v = [0, 0, -100.0]) {
																			cylinder(h = 200, r = 1.8);
																		}
																	}
																	union();
																}
															}
														}
														translate(v = [0, 0, -1.9]) {
															cylinder(h = 1.9, r1 = 1.8, r2 = 3.6);
														}
														translate(v = [0, 0, -12.0]) {
															cylinder(h = 12, r = 1.8);
														}
													}
													union();
												}
											}
										}
										translate(v = [-15.0, -15.0, -100.0]) {
											cylinder(h = 200, r = 3.25);
										}
										translate(v = [-15.0, 15.0, -100.0]) {
											cylinder(h = 200, r = 3.25);
										}
										translate(v = [15.0, -15.0, -100.0]) {
											cylinder(h = 200, r = 3.25);
										}
										translate(v = [15.0, 15.0, -100.0]) {
											cylinder(h = 200, r = 3.25);
										}
										translate(v = [-7.5, 0, -6.0]) {
											cylinder(h = 6, r = 2.0);
										}
										translate(v = [-7.5, 0, -7.0]) {
											cylinder(h = 14, r = 1.8);
										}
										translate(v = [7.5, 0, -6.0]) {
											cylinder(h = 6, r = 2.0);
										}
										translate(v = [7.5, 0, -7.0]) {
											cylinder(h = 14, r = 1.8);
										}
										translate(v = [-2.75, -1.925, -7.0]) {
											cube(size = [5.5, 3.85, 14]);
										}
										translate(v = [-250, -250, -500]) {
											cube(size = [500, 500, 500]);
										}
									}
								}
							}
						}
					}
					union();
				}
			}
		}
	}
	union();
}
