oomlout/oomlout_oobb_part_holder_bearing_version_5/parts/oobb_part_plate_bearing_6704_bearing_size_3_width_3_height_12_depth_motor_gearmotor_01/laser.scad

$fn = 50;

difference() {
	union() {
		translate(v = [0, 0, 0]) {
			rotate(a = [0, 0, 0]) {
				difference() {
					union() {
						translate(v = [0, 0, -6.0]) {
							hull() {
								translate(v = [-17.5, 17.5, 0]) {
									cylinder(h = 12, r = 5);
								}
								translate(v = [17.5, 17.5, 0]) {
									cylinder(h = 12, r = 5);
								}
								translate(v = [-17.5, -17.5, 0]) {
									cylinder(h = 12, r = 5);
								}
								translate(v = [17.5, -17.5, 0]) {
									cylinder(h = 12, r = 5);
								}
							}
						}
					}
					union() {
						translate(v = [0, 0, 0]) {
							rotate(a = [0, 0, 0]) {
								difference() {
									union() {
										translate(v = [0, 0, -2.0]) {
											cylinder(h = 4, r = 13.5);
										}
									}
									union() {
										translate(v = [0, 0, -2.01]) {
											cylinder(h = 4.02, r = 10.0);
										}
									}
								}
							}
						}
						translate(v = [0, 0, 0]) {
							rotate(a = [0, 0, 0]) {
								difference() {
									union() {
										translate(v = [0, 0, -21.0]) {
											cylinder(h = 42, r = 12.25);
										}
									}
									union() {
										translate(v = [0, 0, -21.01]) {
											cylinder(h = 42.02, r = 11.25);
										}
									}
								}
							}
						}
						translate(v = [18.0, 0, -3.0]) {
							rotate(a = [0, 0, 30]) {
								difference() {
									union() {
										linear_extrude(height = 6) {
											polygon(points = [[3.3465999999999996, 0.0], [1.6733000000000002, 2.8982406163050016], [-1.6732999999999991, 2.898240616305002], [-3.3465999999999996, 4.0984029780265316e-16], [-1.6733000000000013, -2.8982406163050016], [1.6732999999999976, -2.8982406163050034]]);
										}
									}
									union();
								}
							}
						}
						translate(v = [0, -18.0, -3.0]) {
							rotate(a = [0, 0, 0]) {
								difference() {
									union() {
										linear_extrude(height = 6) {
											polygon(points = [[3.3465999999999996, 0.0], [1.6733000000000002, 2.8982406163050016], [-1.6732999999999991, 2.898240616305002], [-3.3465999999999996, 4.0984029780265316e-16], [-1.6733000000000013, -2.8982406163050016], [1.6732999999999976, -2.8982406163050034]]);
										}
									}
									union();
								}
							}
						}
						translate(v = [-18.0, 0, -3.0]) {
							rotate(a = [0, 0, 30]) {
								difference() {
									union() {
										linear_extrude(height = 6) {
											polygon(points = [[3.3465999999999996, 0.0], [1.6733000000000002, 2.8982406163050016], [-1.6732999999999991, 2.898240616305002], [-3.3465999999999996, 4.0984029780265316e-16], [-1.6733000000000013, -2.8982406163050016], [1.6732999999999976, -2.8982406163050034]]);
										}
									}
									union();
								}
							}
						}
						translate(v = [0, 18.0, -3.0]) {
							rotate(a = [0, 0, 0]) {
								difference() {
									union() {
										linear_extrude(height = 6) {
											polygon(points = [[3.3465999999999996, 0.0], [1.6733000000000002, 2.8982406163050016], [-1.6732999999999991, 2.898240616305002], [-3.3465999999999996, 4.0984029780265316e-16], [-1.6733000000000013, -2.8982406163050016], [1.6732999999999976, -2.8982406163050034]]);
										}
									}
									union();
								}
							}
						}
						translate(v = [-5.303300858899107, 5.303300858899107, -6.0]) {
							rotate(a = [0, 0, 45.0]) {
								difference() {
									union() {
										linear_extrude(height = 2.5) {
											polygon(points = [[3.1734999999999998, 0.0], [1.5867500000000003, 2.7483316189099156], [-1.5867499999999992, 2.748331618909916], [-3.1734999999999998, 3.886416617094125e-16], [-1.5867500000000012, -2.748331618909915], [1.5867499999999977, -2.748331618909917]]);
										}
									}
									union();
								}
							}
						}
						translate(v = [5.303300858899107, -5.303300858899107, 3.5]) {
							rotate(a = [0, 0, 45.0]) {
								difference() {
									union() {
										linear_extrude(height = 2.5) {
											polygon(points = [[3.1734999999999998, 0.0], [1.5867500000000003, 2.7483316189099156], [-1.5867499999999992, 2.748331618909916], [-3.1734999999999998, 3.886416617094125e-16], [-1.5867500000000012, -2.748331618909915], [1.5867499999999977, -2.748331618909917]]);
										}
									}
									union();
								}
							}
						}
						translate(v = [-15.0, -15.0, -100.0]) {
							cylinder(h = 200, r = 3.0);
						}
						translate(v = [-15.0, 15.0, -100.0]) {
							cylinder(h = 200, r = 3.0);
						}
						translate(v = [15.0, -15.0, -100.0]) {
							cylinder(h = 200, r = 3.0);
						}
						translate(v = [15.0, 15.0, -100.0]) {
							cylinder(h = 200, r = 3.0);
						}
						translate(v = [-7.5, 0, -6.0]) {
							cylinder(h = 6, r = 1.9);
						}
						translate(v = [-7.5, 0, -7.0]) {
							cylinder(h = 14, r = 1.5);
						}
						translate(v = [7.5, 0, -6.0]) {
							cylinder(h = 6, r = 1.9);
						}
						translate(v = [7.5, 0, -7.0]) {
							cylinder(h = 14, r = 1.5);
						}
						translate(v = [18.0, 0, -6.0]) {
							cylinder(h = 3, r = 2.4);
						}
						translate(v = [18.0, 0, 3.0]) {
							cylinder(h = 3, r = 2.4);
						}
						translate(v = [0, -18.0, -6.0]) {
							cylinder(h = 3, r = 2.4);
						}
						translate(v = [0, -18.0, 3.0]) {
							cylinder(h = 3, r = 2.4);
						}
						translate(v = [-18.0, 0, -6.0]) {
							cylinder(h = 3, r = 2.4);
						}
						translate(v = [-18.0, 0, 3.0]) {
							cylinder(h = 3, r = 2.4);
						}
						translate(v = [0, 18.0, -6.0]) {
							cylinder(h = 3, r = 2.4);
						}
						translate(v = [0, 18.0, 3.0]) {
							cylinder(h = 3, r = 2.4);
						}
						translate(v = [-5.303300858899107, 5.303300858899107, -7.0]) {
							cylinder(h = 14, r = 1.5);
						}
						translate(v = [-5.303300858899107, 5.303300858899107, 3.0]) {
							cylinder(h = 3, r = 2.4);
						}
						translate(v = [5.303300858899107, -5.303300858899107, -7.0]) {
							cylinder(h = 14, r = 1.5);
						}
						translate(v = [5.303300858899107, -5.303300858899107, -6.0]) {
							cylinder(h = 3, r = 2.4);
						}
						translate(v = [-2.75, -1.925, -7.0]) {
							cube(size = [5.5, 3.85, 14]);
						}
					}
				}
			}
		}
	}
	union();
}
