oomlout/oomlout_oobb_part_holder_bearing_version_5/parts/oobb_part_plate_bearing_6709_bearing_size_5_width_5_height_12_depth_motor_servo_standard_01_horn_adapter_printed/laser_flat.scad

$fn = 50;

union() {
	translate(v = [0, 0, 0]) {
		projection() {
			intersection() {
				translate(v = [-500, -500, 1.5]) {
					cube(size = [1000, 1000, 0.1]);
				}
				difference() {
					union() {
						translate(v = [0, 0, 0]) {
							rotate(a = [0, 0, 0]) {
								difference() {
									union() {
										translate(v = [0, 0, -6.0]) {
											hull() {
												translate(v = [-32.5, 32.5, 0]) {
													cylinder(h = 12, r = 5);
												}
												translate(v = [32.5, 32.5, 0]) {
													cylinder(h = 12, r = 5);
												}
												translate(v = [-32.5, -32.5, 0]) {
													cylinder(h = 12, r = 5);
												}
												translate(v = [32.5, -32.5, 0]) {
													cylinder(h = 12, r = 5);
												}
											}
										}
									}
									union() {
										translate(v = [0, 0, 0]) {
											rotate(a = [0, 0, 0]) {
												difference() {
													union() {
														translate(v = [0, 0, -3.0]) {
															cylinder(h = 6, r = 27.5);
														}
													}
													union() {
														translate(v = [0, 0, -3.01]) {
															cylinder(h = 6.02, r = 22.5);
														}
													}
												}
											}
										}
										translate(v = [0, 0, 0]) {
											rotate(a = [0, 0, 0]) {
												difference() {
													union() {
														translate(v = [0, 0, -21.0]) {
															cylinder(h = 42, r = 25.5);
														}
													}
													union() {
														translate(v = [0, 0, -21.01]) {
															cylinder(h = 42.02, r = 24.5);
														}
													}
												}
											}
										}
										translate(v = [30.0, 0, -3.0]) {
											rotate(a = [0, 0, 30]) {
												difference() {
													union() {
														linear_extrude(height = 6) {
															polygon(points = [[3.3465999999999996, 0.0], [1.6733000000000002, 2.8982406163050016], [-1.6732999999999991, 2.898240616305002], [-3.3465999999999996, 4.0984029780265316e-16], [-1.6733000000000013, -2.8982406163050016], [1.6732999999999976, -2.8982406163050034]]);
														}
													}
													union();
												}
											}
										}
										translate(v = [0, -30.0, -3.0]) {
											rotate(a = [0, 0, 0]) {
												difference() {
													union() {
														linear_extrude(height = 6) {
															polygon(points = [[3.3465999999999996, 0.0], [1.6733000000000002, 2.8982406163050016], [-1.6732999999999991, 2.898240616305002], [-3.3465999999999996, 4.0984029780265316e-16], [-1.6733000000000013, -2.8982406163050016], [1.6732999999999976, -2.8982406163050034]]);
														}
													}
													union();
												}
											}
										}
										translate(v = [-30.0, 0, -3.0]) {
											rotate(a = [0, 0, 30]) {
												difference() {
													union() {
														linear_extrude(height = 6) {
															polygon(points = [[3.3465999999999996, 0.0], [1.6733000000000002, 2.8982406163050016], [-1.6732999999999991, 2.898240616305002], [-3.3465999999999996, 4.0984029780265316e-16], [-1.6733000000000013, -2.8982406163050016], [1.6732999999999976, -2.8982406163050034]]);
														}
													}
													union();
												}
											}
										}
										translate(v = [0, 30.0, -3.0]) {
											rotate(a = [0, 0, 0]) {
												difference() {
													union() {
														linear_extrude(height = 6) {
															polygon(points = [[3.3465999999999996, 0.0], [1.6733000000000002, 2.8982406163050016], [-1.6732999999999991, 2.898240616305002], [-3.3465999999999996, 4.0984029780265316e-16], [-1.6733000000000013, -2.8982406163050016], [1.6732999999999976, -2.8982406163050034]]);
														}
													}
													union();
												}
											}
										}
										translate(v = [-10.606601717798213, 10.606601717798213, -6.0]) {
											rotate(a = [0, 0, 45.0]) {
												difference() {
													union() {
														linear_extrude(height = 2.5) {
															polygon(points = [[3.1734999999999998, 0.0], [1.5867500000000003, 2.7483316189099156], [-1.5867499999999992, 2.748331618909916], [-3.1734999999999998, 3.886416617094125e-16], [-1.5867500000000012, -2.748331618909915], [1.5867499999999977, -2.748331618909917]]);
														}
													}
													union();
												}
											}
										}
										translate(v = [10.606601717798213, -10.606601717798213, 3.5]) {
											rotate(a = [0, 0, 45.0]) {
												difference() {
													union() {
														linear_extrude(height = 2.5) {
															polygon(points = [[3.1734999999999998, 0.0], [1.5867500000000003, 2.7483316189099156], [-1.5867499999999992, 2.748331618909916], [-3.1734999999999998, 3.886416617094125e-16], [-1.5867500000000012, -2.748331618909915], [1.5867499999999977, -2.748331618909917]]);
														}
													}
													union();
												}
											}
										}
										translate(v = [0, -7.375, -6.0]) {
											rotate(a = [0, 180, 0]) {
												difference() {
													union() {
														translate(v = [0, 0, -1.25]) {
															cylinder(h = 1.25, r = 2.5);
														}
														translate(v = [0, 0, -13.25]) {
															cylinder(h = 12, r = 1.0);
														}
													}
													union();
												}
											}
										}
										translate(v = [0, 7.375, -6.0]) {
											rotate(a = [0, 180, 0]) {
												difference() {
													union() {
														translate(v = [0, 0, -1.25]) {
															cylinder(h = 1.25, r = 2.5);
														}
														translate(v = [0, 0, -13.25]) {
															cylinder(h = 12, r = 1.0);
														}
													}
													union();
												}
											}
										}
										translate(v = [-30.0, -30.0, -100.0]) {
											cylinder(h = 200, r = 3.0);
										}
										translate(v = [-30.0, -15.0, -100.0]) {
											cylinder(h = 200, r = 3.0);
										}
										translate(v = [-30.0, 15.0, -100.0]) {
											cylinder(h = 200, r = 3.0);
										}
										translate(v = [-30.0, 30.0, -100.0]) {
											cylinder(h = 200, r = 3.0);
										}
										translate(v = [-15.0, -30.0, -100.0]) {
											cylinder(h = 200, r = 3.0);
										}
										translate(v = [-15.0, 30.0, -100.0]) {
											cylinder(h = 200, r = 3.0);
										}
										translate(v = [15.0, -30.0, -100.0]) {
											cylinder(h = 200, r = 3.0);
										}
										translate(v = [15.0, 30.0, -100.0]) {
											cylinder(h = 200, r = 3.0);
										}
										translate(v = [30.0, -30.0, -100.0]) {
											cylinder(h = 200, r = 3.0);
										}
										translate(v = [30.0, -15.0, -100.0]) {
											cylinder(h = 200, r = 3.0);
										}
										translate(v = [30.0, 15.0, -100.0]) {
											cylinder(h = 200, r = 3.0);
										}
										translate(v = [30.0, 30.0, -100.0]) {
											cylinder(h = 200, r = 3.0);
										}
										translate(v = [-7.5, 0, -6.0]) {
											cylinder(h = 6, r = 1.9);
										}
										translate(v = [-7.5, 0, -7.0]) {
											cylinder(h = 14, r = 1.5);
										}
										translate(v = [7.5, 0, -6.0]) {
											cylinder(h = 6, r = 1.9);
										}
										translate(v = [7.5, 0, -7.0]) {
											cylinder(h = 14, r = 1.5);
										}
										translate(v = [30.0, 0, -6.0]) {
											cylinder(h = 3, r = 2.4);
										}
										translate(v = [30.0, 0, 3.0]) {
											cylinder(h = 3, r = 2.4);
										}
										translate(v = [0, -30.0, -6.0]) {
											cylinder(h = 3, r = 2.4);
										}
										translate(v = [0, -30.0, 3.0]) {
											cylinder(h = 3, r = 2.4);
										}
										translate(v = [-30.0, 0, -6.0]) {
											cylinder(h = 3, r = 2.4);
										}
										translate(v = [-30.0, 0, 3.0]) {
											cylinder(h = 3, r = 2.4);
										}
										translate(v = [0, 30.0, -6.0]) {
											cylinder(h = 3, r = 2.4);
										}
										translate(v = [0, 30.0, 3.0]) {
											cylinder(h = 3, r = 2.4);
										}
										translate(v = [-10.606601717798213, 10.606601717798213, -7.0]) {
											cylinder(h = 14, r = 1.5);
										}
										translate(v = [-10.606601717798213, 10.606601717798213, 3.0]) {
											cylinder(h = 3, r = 2.4);
										}
										translate(v = [10.606601717798213, -10.606601717798213, -7.0]) {
											cylinder(h = 14, r = 1.5);
										}
										translate(v = [10.606601717798213, -10.606601717798213, -6.0]) {
											cylinder(h = 3, r = 2.4);
										}
										translate(v = [0, 0, -6.0]) {
											cylinder(h = 4, r1 = 2.9, r2 = 2.8);
										}
										translate(v = [0, 0, -7.0]) {
											cylinder(h = 14, r = 1.25);
										}
									}
								}
							}
						}
					}
					union();
				}
			}
		}
	}
}
