oomlout/oomlout_oobb_part_holder_bearing_version_5/navigation_oobb/oobb/part/plate/bearing/6704_bearing_size/3_width/3_height/12_depth/motor_building_block_large_01/3dpr.png

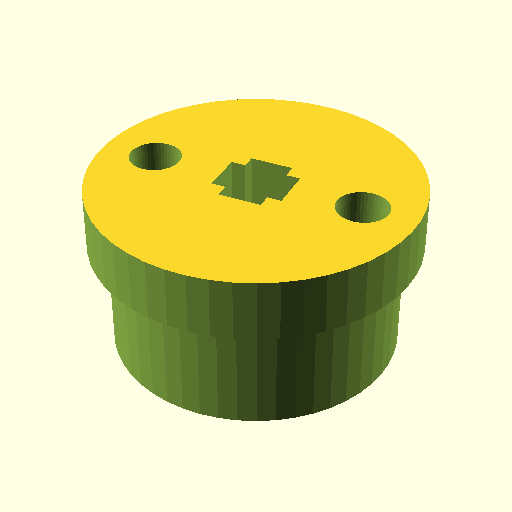
navigation_oobb/oobb/part/plate/bearing/6704_bearing_size/3_width/3_height/12_depth/motor_building_block_large_01/3dpr.png
