oomlout/oomlout_oobb_part_holder_bearing_version_5/navigation_oobb/oobb/part/plate/bearing/6709_bearing_size/5_width/5_height/12_depth/motor_gearmotor_01/working.yaml

bearing_depth: 6
bearing_dimension_source: https://www.cxnjs.com/content/150.html
bearing_inner_diameter: 45
bearing_outer_diameter: 55
bearing_print_radial_clearance: 0.2
bearing_size: '6709'
bip_39_2_word_array:
- glad
- shock
bip_39_2_word_no_space: gladshock
bip_39_2_word_space: glad shock
bip_39_2_word_underscore: glad_shock
bip_39_3_word_array:
- glad
- shock
- ancient
bip_39_3_word_no_space: gladshockancient
bip_39_3_word_space: glad shock ancient
bip_39_3_word_underscore: glad_shock_ancient
bip_39_full_array:
- glad
- shock
- ancient
- gravity
- surprise
- group
- bargain
- novel
- wonder
- amused
- relief
- absent
bip_39_full_no_space: gladshockancientgravitysurprisegroupbargainnovelwonderamusedreliefabsent
bip_39_full_space: glad shock ancient gravity surprise group bargain novel wonder
  amused relief absent
bip_39_full_underscore: glad_shock_ancient_gravity_surprise_group_bargain_novel_wonder_amused_relief_absent
depth: 12
directory: parts/oobb_part_plate_bearing_6709_bearing_size_5_width_5_height_12_depth_motor_gearmotor_01
extra: motor_gearmotor_01
height: 5
id: oobb_part_plate_bearing_6709_bearing_size_5_width_5_height_12_depth_motor_gearmotor_01
id_no_class: oobb_part_plate_bearing_6709_bearing_size_5_width_5_height_12_depth_motor_gearmotor_01
id_no_size: oobb_part_plate_bearing_6709_bearing_size_5_width_5_height_12_depth_motor_gearmotor_01
id_no_type: oobb_part_plate_bearing_6709_bearing_size_5_width_5_height_12_depth_motor_gearmotor_01
id_oobb: oobb_part_plate_bearing_6709_bearing_size_5_width_5_height_12_depth_motor_gearmotor_01
inner_joining_rotation: 45
interior_grid: 0
kwargs:
  bearing_depth: 6
  bearing_inner_diameter: 45
  bearing_outer_diameter: 55
  bearing_print_radial_clearance: 0.2
  bearing_size: '6709'
  body: plate
  depth: 12
  extra: motor_gearmotor_01
  filter: ''
  height: 5
  horn_adapter: ''
  inner_joining_rotation: 45
  interior_grid: 0
  interior_hole_positions: []
  interior_radius_name: m3
  joining_tangent_clearance: 0.01
  modes:
  - 3dpr
  navigation: true
  oobb_name: bearing_plate
  oomp_description_extra: motor_gearmotor_01_shaft_motor_gearmotor_01_extra_12_depth
  oomp_description_main: bearing_plate_5_width_5_height
  oomp_mode: project
  oomp_run: true
  overwrite: true
  prepare_print: true
  print_gap: 10
  shaft: motor_gearmotor_01
  split: true
  split_z: 0
  typ: all
  type: default_bearing_plate
  width: 5
link_github: https://github.com/oomlout/oomlout_oomp_version_1_messy/tree/main/parts/oobb_part_plate_bearing_6709_bearing_size_5_width_5_height_12_depth_motor_gearmotor_01
link_main: https://github.com/oomlout/oomlout_oomp_version_1_messy/tree/main/parts/oobb_part_plate_bearing_6709_bearing_size_5_width_5_height_12_depth_motor_gearmotor_01
link_redirect: https://github.com/oomlout/oomlout_oomp_version_1_messy/tree/main/parts/oobb_part_plate_bearing_6709_bearing_size_5_width_5_height_12_depth_motor_gearmotor_01
md5: 6298c822330da6cdc4acb8fd0106d500
md5_10: 6298c82233
md5_10_upper: 6298C82233
md5_5: 6298c
md5_5_upper: 6298C
md5_6: 6298c8
md5_6_alpha: 3uhu0
md5_6_alpha_upper: 3UHU0
md5_6_upper: 6298C8
name: Oobb Part Plate Bearing 6709 Bearing Size 5 Width 5 Height 12 Depth Motor Gearmotor
  01
name_no_class: Oobb Part Plate Bearing 6709 Bearing Size 5 Width 5 Height 12 Depth
  Motor Gearmotor 01
name_no_size: Oobb Part Plate Bearing 6709 Bearing Size 5 Width 5 Height 12 Depth
  Motor Gearmotor 01
name_no_type: Oobb Part Plate Bearing 6709 Bearing Size 5 Width 5 Height 12 Depth
  Motor Gearmotor 01
name_proper: Oobb Part Plate Bearing 6709 Bearing Size 5 Width 5 Height 12 Depth Motor
  Gearmotor 01
name_space: oobb part plate bearing 6709 bearing size 5 width 5 height 12 depth motor
  gearmotor 01
name_upper: OOBB PART PLATE BEARING 6709 BEARING SIZE 5 WIDTH 5 HEIGHT 12 DEPTH MOTOR
  GEARMOTOR 01
oobb_details:
  bearing_depth: 6
  bearing_inner_diameter: 45
  bearing_outer_diameter: 55
  bearing_print_radial_clearance: 0.2
  bearing_size: '6709'
  body: plate
  depth: 12
  extra: motor_gearmotor_01
  height: 5
  horn_adapter: ''
  inner_joining_rotation: 45
  interior_grid: 0
  interior_hole_positions: []
  interior_radius_name: m3
  joining_tangent_clearance: 0.01
  oobb_name: bearing_plate
  prepare_print: true
  print_gap: 10
  shaft: motor_gearmotor_01
  split: true
  split_z: 0
  width: 5
oobb_name: bearing_plate
oomlout_ai_roboclick_1:
  actions:
  - command: text_jinja_template
    convert_to_pdf: false
    convert_to_png: false
    dict_data:
      bearing_depth: 6
      bearing_dimension_source: https://www.cxnjs.com/content/150.html
      bearing_inner_diameter: 45
      bearing_outer_diameter: 55
      bearing_print_radial_clearance: 0.2
      bearing_size: '6709'
      depth: 12
      directory: parts\oobb_part_plate_bearing_6709_bearing_size_5_width_5_height_12_depth_motor_gearmotor_01
      extra: motor_gearmotor_01
      height: 5
      id: oobb_part_plate_bearing_6709_bearing_size_5_width_5_height_12_depth_motor_gearmotor_01
      inner_joining_rotation: 45
      interior_grid: 0
      name: oobb_part_plate_bearing_6709_bearing_size_5_width_5_height_12_depth_motor_gearmotor_01
      name_proper: Oobb Part Plate Bearing 6709 Bearing Size 5 Width 5 Height 12 Depth
        Motor Gearmotor 01
      name_space: oobb part plate bearing 6709 bearing size 5 width 5 height 12 depth
        motor gearmotor 01
      name_upper: OOBB PART PLATE BEARING 6709 BEARING SIZE 5 WIDTH 5 HEIGHT 12 DEPTH
        MOTOR GEARMOTOR 01
      oobb_details:
        bearing_depth: 6
        bearing_inner_diameter: 45
        bearing_outer_diameter: 55
        bearing_print_radial_clearance: 0.2
        bearing_size: '6709'
        body: plate
        depth: 12
        extra: motor_gearmotor_01
        height: 5
        horn_adapter: ''
        inner_joining_rotation: 45
        interior_grid: 0
        interior_hole_positions: []
        interior_radius_name: m3
        joining_tangent_clearance: 0.01
        oobb_name: bearing_plate
        prepare_print: true
        print_gap: 10
        shaft: motor_gearmotor_01
        split: true
        split_z: 0
        width: 5
      shaft: motor_gearmotor_01
      taxonomy_1: oobb
      taxonomy_10: ''
      taxonomy_11: ''
      taxonomy_12: ''
      taxonomy_13: ''
      taxonomy_14: ''
      taxonomy_15: ''
      taxonomy_2: part
      taxonomy_3: plate
      taxonomy_4: bearing
      taxonomy_5: 6709_bearing_size
      taxonomy_6: 5_width
      taxonomy_7: 5_height
      taxonomy_8: 12_depth
      taxonomy_9: motor_gearmotor_01
      url_chat: ''
      width: 5
    dict_data_files: {}
    dict_data_files_exists: {}
    file_output: label_oomp.svg
    file_template: C:\gh\oomlout_oobb_part_plate_bearing_version_5\source_file\template_jinja\template_jinja_label_oomlout_76_2_mm_50_8_mm\working.svg.j2
    search_and_replace: []
  file_test: label_oomp.pdf
  retries_until_complete: 0
oomp_key: oomp_oobb_part_plate_bearing_6709_bearing_size_5_width_5_height_12_depth_motor_gearmotor_01
project_name: C:\gh\oomlout_oobb_part_plate_bearing_version_5
shaft: motor_gearmotor_01
taxonomy_1: oobb
taxonomy_10: ''
taxonomy_11: ''
taxonomy_12: ''
taxonomy_13: ''
taxonomy_14: ''
taxonomy_15: ''
taxonomy_1_capital: Oobb
taxonomy_1_first_letter: o
taxonomy_1_first_letter_upper: O
taxonomy_1_length_1: o
taxonomy_1_length_2: oo
taxonomy_1_length_3: oob
taxonomy_1_length_4: oobb
taxonomy_1_length_5: oobb
taxonomy_1_upper: OOBB
taxonomy_1_upper_length_1: O
taxonomy_1_upper_length_2: OO
taxonomy_1_upper_length_3: OOB
taxonomy_1_upper_length_4: OOBB
taxonomy_1_upper_length_5: OOBB
taxonomy_2: part
taxonomy_2_capital: Part
taxonomy_2_first_letter: p
taxonomy_2_first_letter_upper: P
taxonomy_2_length_1: p
taxonomy_2_length_2: pa
taxonomy_2_length_3: par
taxonomy_2_length_4: part
taxonomy_2_length_5: part
taxonomy_2_upper: PART
taxonomy_2_upper_length_1: P
taxonomy_2_upper_length_2: PA
taxonomy_2_upper_length_3: PAR
taxonomy_2_upper_length_4: PART
taxonomy_2_upper_length_5: PART
taxonomy_3: plate
taxonomy_3_capital: Plate
taxonomy_3_first_letter: p
taxonomy_3_first_letter_upper: P
taxonomy_3_length_1: p
taxonomy_3_length_2: pl
taxonomy_3_length_3: pla
taxonomy_3_length_4: plat
taxonomy_3_length_5: plate
taxonomy_3_upper: PLATE
taxonomy_3_upper_length_1: P
taxonomy_3_upper_length_2: PL
taxonomy_3_upper_length_3: PLA
taxonomy_3_upper_length_4: PLAT
taxonomy_3_upper_length_5: PLATE
taxonomy_4: bearing
taxonomy_4_capital: Bearing
taxonomy_4_first_letter: b
taxonomy_4_first_letter_upper: B
taxonomy_4_length_1: b
taxonomy_4_length_2: be
taxonomy_4_length_3: bea
taxonomy_4_length_4: bear
taxonomy_4_length_5: beari
taxonomy_4_upper: BEARING
taxonomy_4_upper_length_1: B
taxonomy_4_upper_length_2: BE
taxonomy_4_upper_length_3: BEA
taxonomy_4_upper_length_4: BEAR
taxonomy_4_upper_length_5: BEARI
taxonomy_5: 6709_bearing_size
taxonomy_5_capital: 6709 Bearing Size
taxonomy_5_first_letter: '6'
taxonomy_5_first_letter_upper: '6'
taxonomy_5_length_1: '6'
taxonomy_5_length_2: '67'
taxonomy_5_length_3: '670'
taxonomy_5_length_4: '6709'
taxonomy_5_length_5: '6709_'
taxonomy_5_upper: 6709_BEARING_SIZE
taxonomy_5_upper_length_1: '6'
taxonomy_5_upper_length_2: '67'
taxonomy_5_upper_length_3: '670'
taxonomy_5_upper_length_4: '6709'
taxonomy_5_upper_length_5: '6709_'
taxonomy_6: 5_width
taxonomy_6_capital: 5 Width
taxonomy_6_first_letter: '5'
taxonomy_6_first_letter_upper: '5'
taxonomy_6_length_1: '5'
taxonomy_6_length_2: '5_'
taxonomy_6_length_3: 5_w
taxonomy_6_length_4: 5_wi
taxonomy_6_length_5: 5_wid
taxonomy_6_upper: 5_WIDTH
taxonomy_6_upper_length_1: '5'
taxonomy_6_upper_length_2: '5_'
taxonomy_6_upper_length_3: 5_W
taxonomy_6_upper_length_4: 5_WI
taxonomy_6_upper_length_5: 5_WID
taxonomy_7: 5_height
taxonomy_7_capital: 5 Height
taxonomy_7_first_letter: '5'
taxonomy_7_first_letter_upper: '5'
taxonomy_7_length_1: '5'
taxonomy_7_length_2: '5_'
taxonomy_7_length_3: 5_h
taxonomy_7_length_4: 5_he
taxonomy_7_length_5: 5_hei
taxonomy_7_upper: 5_HEIGHT
taxonomy_7_upper_length_1: '5'
taxonomy_7_upper_length_2: '5_'
taxonomy_7_upper_length_3: 5_H
taxonomy_7_upper_length_4: 5_HE
taxonomy_7_upper_length_5: 5_HEI
taxonomy_8: 12_depth
taxonomy_8_capital: 12 Depth
taxonomy_8_first_letter: '1'
taxonomy_8_first_letter_upper: '1'
taxonomy_8_length_1: '1'
taxonomy_8_length_2: '12'
taxonomy_8_length_3: '12_'
taxonomy_8_length_4: 12_d
taxonomy_8_length_5: 12_de
taxonomy_8_upper: 12_DEPTH
taxonomy_8_upper_length_1: '1'
taxonomy_8_upper_length_2: '12'
taxonomy_8_upper_length_3: '12_'
taxonomy_8_upper_length_4: 12_D
taxonomy_8_upper_length_5: 12_DE
taxonomy_9: motor_gearmotor_01
taxonomy_9_capital: Motor Gearmotor 01
taxonomy_9_first_letter: m
taxonomy_9_first_letter_upper: M
taxonomy_9_length_1: m
taxonomy_9_length_2: mo
taxonomy_9_length_3: mot
taxonomy_9_length_4: moto
taxonomy_9_length_5: motor
taxonomy_9_upper: MOTOR_GEARMOTOR_01
taxonomy_9_upper_length_1: M
taxonomy_9_upper_length_2: MO
taxonomy_9_upper_length_3: MOT
taxonomy_9_upper_length_4: MOTO
taxonomy_9_upper_length_5: MOTOR
url_chat: ''
width: 5
