oomlout/oomlout_oobb_part_holder_bearing_version_5/navigation_oobb/oobb/part/plate/bearing/6709_bearing_size/5_width/5_height/12_depth/motor_servo_standard_01_horn_adapter_screws/thing.yaml

bearing_depth: 6
bearing_dimension_source: https://www.cxnjs.com/content/150.html
bearing_inner_diameter: 45
bearing_outer_diameter: 55
bearing_print_radial_clearance: 0.2
bearing_size: '6709'
bip_39_2_word_array:
- shy
- cliff
bip_39_2_word_no_space: shycliff
bip_39_2_word_space: shy cliff
bip_39_2_word_underscore: shy_cliff
bip_39_3_word_array:
- shy
- cliff
- hip
bip_39_3_word_no_space: shycliffhip
bip_39_3_word_space: shy cliff hip
bip_39_3_word_underscore: shy_cliff_hip
bip_39_full_array:
- shy
- cliff
- hip
- onion
- arena
- shy
- obtain
- soda
- claw
- say
- inform
- mean
bip_39_full_no_space: shycliffhiponionarenashyobtainsodaclawsayinformmean
bip_39_full_space: shy cliff hip onion arena shy obtain soda claw say inform mean
bip_39_full_underscore: shy_cliff_hip_onion_arena_shy_obtain_soda_claw_say_inform_mean
body: cylinder
depth: 12
directory: parts/oobb_part_plate_bearing_6709_bearing_size_5_width_5_height_12_depth_motor_servo_standard_01_horn_adapter_screws
extra: motor_servo_standard_01_horn_adapter_screws
height: 5
horn_adapter: screws
id: oobb_part_plate_bearing_6709_bearing_size_5_width_5_height_12_depth_motor_servo_standard_01_horn_adapter_screws
id_no_class: oobb_part_plate_bearing_6709_bearing_size_5_width_5_height_12_depth_motor_servo_standard_01_horn_adapter_screws
id_no_size: oobb_part_plate_bearing_6709_bearing_size_5_width_5_height_12_depth_motor_servo_standard_01_horn_adapter_screws
id_no_type: oobb_part_plate_bearing_6709_bearing_size_5_width_5_height_12_depth_motor_servo_standard_01_horn_adapter_screws
id_oobb: oobb_part_plate_bearing_6709_bearing_size_5_width_5_height_12_depth_motor_servo_standard_01_horn_adapter_screws
inner_joining_rotation: 45
interior_grid: 0
kwargs:
  bearing_depth: 6
  bearing_inner_diameter: 45
  bearing_outer_diameter: 55
  bearing_print_radial_clearance: 0.2
  bearing_size: '6709'
  body: cylinder
  depth: 12
  extra: motor_servo_standard_01_horn_adapter_screws
  filter: ''
  height: 5
  horn_adapter: screws
  inner_joining_rotation: 45
  interior_grid: 0
  interior_hole_positions: []
  interior_radius_name: m3
  joining_tangent_clearance: 0.01
  modes:
  - 3dpr
  navigation: true
  oobb_name: bearing_plate
  oomp_description_extra: motor_servo_standard_01_shaft_motor_servo_standard_01_horn_adapter_screws_extra_12_depth
  oomp_description_main: bearing_plate_5_width_5_height
  oomp_mode: project
  oomp_run: true
  overwrite: true
  prepare_print: true
  print_gap: 10
  shaft: motor_servo_standard_01
  split: true
  split_z: 0.5
  typ: all
  type: default_bearing_plate
  width: 5
link_github: https://github.com/oomlout/oomlout_oomp_version_1_messy/tree/main/parts/oobb_part_plate_bearing_6709_bearing_size_5_width_5_height_12_depth_motor_servo_standard_01_h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
link_main: https://github.com/oomlout/oomlout_oomp_version_1_messy/tree/main/parts/oobb_part_plate_bearing_6709_bearing_size_5_width_5_height_12_depth_motor_servo_standard_01_h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
link_redirect: https://github.com/oomlout/oomlout_oomp_version_1_messy/tree/main/parts/oobb_part_plate_bearing_6709_bearing_size_5_width_5_height_12_depth_motor_servo_standard_01_h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
md5: c7855dafcd60b78f2626712a17fdce44
md5_10: c7855dafcd
md5_10_upper: C7855DAFCD
md5_5: c7855
md5_5_upper: C7855
md5_6: c7855d
md5_6_alpha: 7s9ct
md5_6_alpha_upper: 7S9CT
md5_6_upper: C7855D
name: Oobb Part Plate Bearing 6709 Bearing Size 5 Width 5 Height 12 Depth Motor Servo
  Standard 01 Horn Adapter Screws
name_no_class: Oobb Part Plate Bearing 6709 Bearing Size 5 Width 5 Height 12 Depth
  Motor Servo Standard 01 Horn Adapter Screws
name_no_size: Oobb Part Plate Bearing 6709 Bearing Size 5 Width 5 Height 12 Depth
  Motor Servo Standard 01 Horn Adapter Screws
name_no_type: Oobb Part Plate Bearing 6709 Bearing Size 5 Width 5 Height 12 Depth
  Motor Servo Standard 01 Horn Adapter Screws
name_proper: Oobb Part Plate Bearing 6709 Bearing Size 5 Width 5 Height 12 Depth Motor
  Servo Standard 01 Horn Adapter Screws
name_space: oobb part plate bearing 6709 bearing size 5 width 5 height 12 depth motor
  servo standard 01 horn adapter screws
name_upper: OOBB PART PLATE BEARING 6709 BEARING SIZE 5 WIDTH 5 HEIGHT 12 DEPTH MOTOR
  SERVO STANDARD 01 HORN ADAPTER SCREWS
oobb_details:
  bearing_depth: 6
  bearing_inner_diameter: 45
  bearing_outer_diameter: 55
  bearing_print_radial_clearance: 0.2
  bearing_size: '6709'
  body: cylinder
  depth: 12
  extra: motor_servo_standard_01_horn_adapter_screws
  height: 5
  horn_adapter: screws
  inner_joining_rotation: 45
  interior_grid: 0
  interior_hole_positions: []
  interior_radius_name: m3
  joining_tangent_clearance: 0.01
  oobb_name: bearing_plate
  prepare_print: true
  print_gap: 10
  shaft: motor_servo_standard_01
  split: true
  split_z: 0.5
  width: 5
oobb_name: bearing_plate
oomlout_ai_roboclick_1:
  actions:
  - command: text_jinja_template
    convert_to_pdf: false
    convert_to_png: false
    dict_data:
      bearing_depth: 6
      bearing_dimension_source: https://www.cxnjs.com/content/150.html
      bearing_inner_diameter: 45
      bearing_outer_diameter: 55
      bearing_print_radial_clearance: 0.2
      bearing_size: '6709'
      body: cylinder
      depth: 12
      directory: parts\oobb_part_plate_bearing_6709_bearing_size_5_width_5_height_12_depth_motor_servo_standard_01_horn_adapter_screws
      extra: motor_servo_standard_01_horn_adapter_screws
      height: 5
      horn_adapter: screws
      id: oobb_part_plate_bearing_6709_bearing_size_5_width_5_height_12_depth_motor_servo_standard_01_horn_adapter_screws
      inner_joining_rotation: 45
      interior_grid: 0
      name: oobb_part_plate_bearing_6709_bearing_size_5_width_5_height_12_depth_motor_servo_standard_01_horn_adapter_screws
      name_proper: Oobb Part Plate Bearing 6709 Bearing Size 5 Width 5 Height 12 Depth
        Motor Servo Standard 01 Horn Adapter Screws
      name_space: oobb part plate bearing 6709 bearing size 5 width 5 height 12 depth
        motor servo standard 01 horn adapter screws
      name_upper: OOBB PART PLATE BEARING 6709 BEARING SIZE 5 WIDTH 5 HEIGHT 12 DEPTH
        MOTOR SERVO STANDARD 01 HORN ADAPTER SCREWS
      oobb_details:
        bearing_depth: 6
        bearing_inner_diameter: 45
        bearing_outer_diameter: 55
        bearing_print_radial_clearance: 0.2
        bearing_size: '6709'
        body: cylinder
        depth: 12
        extra: motor_servo_standard_01_horn_adapter_screws
        height: 5
        horn_adapter: screws
        inner_joining_rotation: 45
        interior_grid: 0
        interior_hole_positions: []
        interior_radius_name: m3
        joining_tangent_clearance: 0.01
        oobb_name: bearing_plate
        prepare_print: true
        print_gap: 10
        shaft: motor_servo_standard_01
        split: true
        split_z: 0.5
        width: 5
      shaft: motor_servo_standard_01
      split_z: 0.5
      taxonomy_1: oobb
      taxonomy_10: ''
      taxonomy_11: ''
      taxonomy_12: ''
      taxonomy_13: ''
      taxonomy_14: ''
      taxonomy_15: ''
      taxonomy_2: part
      taxonomy_3: plate
      taxonomy_4: bearing
      taxonomy_5: 6709_bearing_size
      taxonomy_6: 5_width
      taxonomy_7: 5_height
      taxonomy_8: 12_depth
      taxonomy_9: motor_servo_standard_01_horn_adapter_screws
      url_chat: ''
      width: 5
    dict_data_files: {}
    dict_data_files_exists: {}
    file_output: label_oomp.svg
    file_template: C:\gh\oomlout_oobb_part_plate_bearing_version_5\source_file\template_jinja\template_jinja_label_oomlout_76_2_mm_50_8_mm\working.svg.j2
    search_and_replace: []
  file_test: label_oomp.pdf
  retries_until_complete: 0
oomp_key: oomp_oobb_part_plate_bearing_6709_bearing_size_5_width_5_height_12_depth_motor_servo_standard_01_horn_adapter_screws
project_name: C:\gh\oomlout_oobb_part_plate_bearing_version_5
shaft: motor_servo_standard_01
split_z: 0.5
taxonomy_1: oobb
taxonomy_10: ''
taxonomy_11: ''
taxonomy_12: ''
taxonomy_13: ''
taxonomy_14: ''
taxonomy_15: ''
taxonomy_1_capital: Oobb
taxonomy_1_first_letter: o
taxonomy_1_first_letter_upper: O
taxonomy_1_length_1: o
taxonomy_1_length_2: oo
taxonomy_1_length_3: oob
taxonomy_1_length_4: oobb
taxonomy_1_length_5: oobb
taxonomy_1_upper: OOBB
taxonomy_1_upper_length_1: O
taxonomy_1_upper_length_2: OO
taxonomy_1_upper_length_3: OOB
taxonomy_1_upper_length_4: OOBB
taxonomy_1_upper_length_5: OOBB
taxonomy_2: part
taxonomy_2_capital: Part
taxonomy_2_first_letter: p
taxonomy_2_first_letter_upper: P
taxonomy_2_length_1: p
taxonomy_2_length_2: pa
taxonomy_2_length_3: par
taxonomy_2_length_4: part
taxonomy_2_length_5: part
taxonomy_2_upper: PART
taxonomy_2_upper_length_1: P
taxonomy_2_upper_length_2: PA
taxonomy_2_upper_length_3: PAR
taxonomy_2_upper_length_4: PART
taxonomy_2_upper_length_5: PART
taxonomy_3: plate
taxonomy_3_capital: Plate
taxonomy_3_first_letter: p
taxonomy_3_first_letter_upper: P
taxonomy_3_length_1: p
taxonomy_3_length_2: pl
taxonomy_3_length_3: pla
taxonomy_3_length_4: plat
taxonomy_3_length_5: plate
taxonomy_3_upper: PLATE
taxonomy_3_upper_length_1: P
taxonomy_3_upper_length_2: PL
taxonomy_3_upper_length_3: PLA
taxonomy_3_upper_length_4: PLAT
taxonomy_3_upper_length_5: PLATE
taxonomy_4: bearing
taxonomy_4_capital: Bearing
taxonomy_4_first_letter: b
taxonomy_4_first_letter_upper: B
taxonomy_4_length_1: b
taxonomy_4_length_2: be
taxonomy_4_length_3: bea
taxonomy_4_length_4: bear
taxonomy_4_length_5: beari
taxonomy_4_upper: BEARING
taxonomy_4_upper_length_1: B
taxonomy_4_upper_length_2: BE
taxonomy_4_upper_length_3: BEA
taxonomy_4_upper_length_4: BEAR
taxonomy_4_upper_length_5: BEARI
taxonomy_5: 6709_bearing_size
taxonomy_5_capital: 6709 Bearing Size
taxonomy_5_first_letter: '6'
taxonomy_5_first_letter_upper: '6'
taxonomy_5_length_1: '6'
taxonomy_5_length_2: '67'
taxonomy_5_length_3: '670'
taxonomy_5_length_4: '6709'
taxonomy_5_length_5: '6709_'
taxonomy_5_upper: 6709_BEARING_SIZE
taxonomy_5_upper_length_1: '6'
taxonomy_5_upper_length_2: '67'
taxonomy_5_upper_length_3: '670'
taxonomy_5_upper_length_4: '6709'
taxonomy_5_upper_length_5: '6709_'
taxonomy_6: 5_width
taxonomy_6_capital: 5 Width
taxonomy_6_first_letter: '5'
taxonomy_6_first_letter_upper: '5'
taxonomy_6_length_1: '5'
taxonomy_6_length_2: '5_'
taxonomy_6_length_3: 5_w
taxonomy_6_length_4: 5_wi
taxonomy_6_length_5: 5_wid
taxonomy_6_upper: 5_WIDTH
taxonomy_6_upper_length_1: '5'
taxonomy_6_upper_length_2: '5_'
taxonomy_6_upper_length_3: 5_W
taxonomy_6_upper_length_4: 5_WI
taxonomy_6_upper_length_5: 5_WID
taxonomy_7: 5_height
taxonomy_7_capital: 5 Height
taxonomy_7_first_letter: '5'
taxonomy_7_first_letter_upper: '5'
taxonomy_7_length_1: '5'
taxonomy_7_length_2: '5_'
taxonomy_7_length_3: 5_h
taxonomy_7_length_4: 5_he
taxonomy_7_length_5: 5_hei
taxonomy_7_upper: 5_HEIGHT
taxonomy_7_upper_length_1: '5'
taxonomy_7_upper_length_2: '5_'
taxonomy_7_upper_length_3: 5_H
taxonomy_7_upper_length_4: 5_HE
taxonomy_7_upper_length_5: 5_HEI
taxonomy_8: 12_depth
taxonomy_8_capital: 12 Depth
taxonomy_8_first_letter: '1'
taxonomy_8_first_letter_upper: '1'
taxonomy_8_length_1: '1'
taxonomy_8_length_2: '12'
taxonomy_8_length_3: '12_'
taxonomy_8_length_4: 12_d
taxonomy_8_length_5: 12_de
taxonomy_8_upper: 12_DEPTH
taxonomy_8_upper_length_1: '1'
taxonomy_8_upper_length_2: '12'
taxonomy_8_upper_length_3: '12_'
taxonomy_8_upper_length_4: 12_D
taxonomy_8_upper_length_5: 12_DE
taxonomy_9: motor_servo_standard_01_horn_adapter_screws
taxonomy_9_capital: Motor Servo Standard 01 Horn Adapter Screws
taxonomy_9_first_letter: m
taxonomy_9_first_letter_upper: M
taxonomy_9_length_1: m
taxonomy_9_length_2: mo
taxonomy_9_length_3: mot
taxonomy_9_length_4: moto
taxonomy_9_length_5: motor
taxonomy_9_upper: MOTOR_SERVO_STANDARD_01_HORN_ADAPTER_SCREWS
taxonomy_9_upper_length_1: M
taxonomy_9_upper_length_2: MO
taxonomy_9_upper_length_3: MOT
taxonomy_9_upper_length_4: MOTO
taxonomy_9_upper_length_5: MOTOR
thing:
  bearing_depth: 6
  bearing_dimension_source: https://www.cxnjs.com/content/150.html
  bearing_inner_diameter: 45
  bearing_outer_diameter: 55
  bearing_print_radial_clearance: 0.2
  bearing_size: '6709'
  bip_39_2_word_array:
  - shy
  - cliff
  bip_39_2_word_no_space: shycliff
  bip_39_2_word_space: shy cliff
  bip_39_2_word_underscore: shy_cliff
  bip_39_3_word_array:
  - shy
  - cliff
  - hip
  bip_39_3_word_no_space: shycliffhip
  bip_39_3_word_space: shy cliff hip
  bip_39_3_word_underscore: shy_cliff_hip
  bip_39_full_array:
  - shy
  - cliff
  - hip
  - onion
  - arena
  - shy
  - obtain
  - soda
  - claw
  - say
  - inform
  - mean
  bip_39_full_no_space: shycliffhiponionarenashyobtainsodaclawsayinformmean
  bip_39_full_space: shy cliff hip onion arena shy obtain soda claw say inform mean
  bip_39_full_underscore: shy_cliff_hip_onion_arena_shy_obtain_soda_claw_say_inform_mean
  body: cylinder
  classification: oobb
  color: ''
  components:
  - inclusion: 3dpr
    objects:
    - inclusion: 3dpr
      objects:
      - - depth: 12
          h: 12
          height: 5
          inclusion: laser
          pos: &id001
          - 0
          - 0
          - -6.0
          r: 24.5
          shape: cylinder
          type: positive
          width: 5
        - depth: 12
          h: 12
          height: 5
          inclusion: 3dpr
          pos: *id001
          r: 24.5
          shape: cylinder
          type: positive
          width: 5
        - depth: 12
          h: 12
          height: 5
          inclusion: 'true'
          pos: *id001
          r: 24.5
          shape: cylinder
          type: positive
          width: 5
      - inclusion: 3dpr
        objects:
        - - depth: 6
            h: 6
            inclusion: laser
            pos: &id002
            - 0
            - 0
            - -3.0
            r: 27.7
            shape: cylinder
            type: positive
          - depth: 6
            h: 6
            inclusion: 3dpr
            pos: *id002
            r: 27.7
            shape: cylinder
            type: positive
          - depth: 6
            h: 6
            inclusion: 'true'
            pos: *id002
            r: 27.7
            shape: cylinder
            type: positive
        - - depth: 6.02
            h: 6.02
            inclusion: laser
            pos: &id003
            - 0
            - 0
            - -3.01
            r: 22.5
            shape: cylinder
            type: negative
          - depth: 6.02
            h: 6.02
            inclusion: 3dpr
            pos: *id003
            r: 22.5
            shape: cylinder
            type: negative
          - depth: 6.02
            h: 6.02
            inclusion: 'true'
            pos: *id003
            r: 22.5
            shape: cylinder
            type: negative
        pos:
        - 0
        - 0
        - 0
        rot:
        - 0
        - 0
        - 0
        type: rotation
        typetype: negative
      - inclusion: 3dpr
        objects:
        - - depth: 42
            h: 42
            inclusion: laser
            pos: &id004
            - 0
            - 0
            - -21.0
            r: 25.6
            shape: cylinder
            type: positive
          - depth: 42
            h: 42
            inclusion: 3dpr
            pos: *id004
            r: 25.6
            shape: cylinder
            type: positive
          - depth: 42
            h: 42
            inclusion: 'true'
            pos: *id004
            r: 25.6
            shape: cylinder
            type: positive
        - - depth: 42.02
            h: 42.02
            inclusion: laser
            pos: &id005
            - 0
            - 0
            - -21.01
            r: 24.6
            shape: cylinder
            type: negative
          - depth: 42.02
            h: 42.02
            inclusion: 3dpr
            pos: *id005
            r: 24.6
            shape: cylinder
            type: negative
          - depth: 42.02
            h: 42.02
            inclusion: 'true'
            pos: *id005
            r: 24.6
            shape: cylinder
            type: negative
        pos:
        - 0
        - 0
        - 0
        rot:
        - 0
        - 0
        - 0
        type: rotation
        typetype: negative
      - - - h: 200
            inclusion: laser
            m: ''
            pos:
            - -30.0
            - -30.0
            - -100.0
            r: 3.0
            shape: cylinder
            type: negative
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
    type: negative
    zz: center
  - height: 5
    holes: perimeter_miss_middle
    inclusion: 3dpr
    mode: 3dpr
    pos:
    - 0
    - 0
    - 0
    radius_name: m6
    shape: oobb_holes
    type: negative
    width: 5
  - depth: 6
    mode: 3dpr
    pos:
    - -7.5
    - 0
    - -3.0
    radius_name: plate_bearing_insert_radius
    shape: oobb_cylinder
    type: negative
    zz: center
  - depth: 14
    mode: 3dpr
    pos:
    - -7.5
    - 0
    - -7.0
    radius_name: m3
    shape: oobb_hole
    type: negative
  - depth: 6
    mode: 3dpr
    pos:
    - 7.5
    - 0
    - -3.0
    radius_name: plate_bearing_insert_radius
    shape: oobb_cylinder
    type: negative
    zz: center
  - depth: 14
    mode: 3dpr
    pos:
    - 7.5
    - 0
    - -7.0
    radius_name: m3
    shape: oobb_hole
    type: negative
  - depth: 4
    mode: 3dpr
    pos:
    - 0
    - 0
    - -6.0
    radius_1: 2.9
    radius_2: 2.8
    shape: oobb_cylinder
    type: negative
    zz: bottom
  - depth: 14
    mode: 3dpr
    pos:
    - 0
    - 0
    - -7.0
    radius_name: m2d5
    shape: oobb_hole
    type: negative
  - depth: 12
    loose:
    - screw
    mode: 3dpr
    overhang: true
    pos:
    - 0
    - -7.375
    - -6.0
    radius_name: m2
    rot:
    - 0
    - 180
    - 0
    shape: oobb_screw_self_tapping
    type: negative
    zz: top
  - depth: 12
    loose:
    - screw
    mode: 3dpr
    overhang: true
    pos:
    - 0
    - 7.375
    - -6.0
    radius_name: m2
    rot:
    - 0
    - 180
    - 0
    shape: oobb_screw_self_tapping
    type: negative
    zz: top
  components_string:
  - oobb_cylinder_shape_positive_type_plate_bearing_adapter_radius_radius_name_12_depth_5_width_5_height_true_extra_mm_false_holes_center_zz_3dpr_mode
  - oobb_holes_shape_negative_type_m6_radius_name_5_width_5_height_perimeter_miss_middle_holes_3dpr_mode
  - oobb_cylinder_shape_negative_type_plate_bearing_insert_radius_radius_name_6_depth_-7.5_0_-3.0_pos_center_zz_3dpr_mode
  - oobb_hole_shape_negative_type_m3_radius_name_14_depth_-7.5_0_-7.0_pos_3dpr_mode
  - oobb_cylinder_shape_negative_type_plate_bearing_insert_radius_radius_name_6_depth_7.5_0_-3.0_pos_center_zz_3dpr_mode
  - oobb_hole_shape_negative_type_m3_radius_name_14_depth_7.5_0_-7.0_pos_3dpr_mode
  - oobb_cylinder_shape_negative_type_4_depth_0_0_-6.0_pos_2.9_radius_1_2.8_radius_2_bottom_zz_3dpr_mode
  - oobb_hole_shape_negative_type_m2d5_radius_name_14_depth_0_0_-7.0_pos_3dpr_mode
  - oobb_screw_self_tapping_shape_negative_type_m2_radius_name_12_depth_0_-7.375_-6.0_pos_0_180_0_rot_top_zz_'screw'_loose_true_overhang_3dpr_mode
  - oobb_screw_self_tapping_shape_negative_type_m2_radius_name_12_depth_0_7.375_-6.0_pos_0_180_0_rot_top_zz_'screw'_loose_true_overhang_3dpr_mode
  depth: 12
  description: default bearing plate 5x5x0
  description_extra: motor_servo_standard_01_shaft_motor_servo_standard_01_horn_adapter_screws_extra_12_depth
  description_main: 5_width_5_height
  directory: parts/oobb_part_plate_bearing_6709_bearing_size_5_width_5_height_12_depth_motor_servo_standard_01_horn_adapter_screws
  extra: motor_servo_standard_01_horn_adapter_screws
  height: 5
  height_mm: 74
  horn_adapter: screws
  id: oobb_part_plate_bearing_6709_bearing_size_5_width_5_height_12_depth_motor_servo_standard_01_horn_adapter_screws
  id_no_class: oobb_part_plate_bearing_6709_bearing_size_5_width_5_height_12_depth_motor_servo_standard_01_horn_adapter_screws
  id_no_size: oobb_part_plate_bearing_6709_bearing_size_5_width_5_height_12_depth_motor_servo_standard_01_horn_adapter_screws
  id_no_type: oobb_part_plate_bearing_6709_bearing_size_5_width_5_height_12_depth_motor_servo_standard_01_horn_adapter_screws
  inner_joining_rotation: 45
  interior_grid: 0
  kwargs:
    bearing_depth: 6
    bearing_inner_diameter: 45
    bearing_outer_diameter: 55
    bearing_print_radial_clearance: 0.2
    bearing_size: '6709'
    body: cylinder
    depth: 12
    extra: motor_servo_standard_01_horn_adapter_screws
    filter: ''
    height: 5
    horn_adapter: screws
    inner_joining_rotation: 45
    interior_grid: 0
    interior_hole_positions: []
    interior_radius_name: m3
    joining_tangent_clearance: 0.01
    modes:
    - 3dpr
    navigation: true
    oobb_name: bearing_plate
    oomp_description_extra: motor_servo_standard_01_shaft_motor_servo_standard_01_horn_adapter_screws_extra_12_depth
    oomp_description_main: bearing_plate_5_width_5_height
    oomp_mode: project
    oomp_run: true
    overwrite: true
    prepare_print: true
    print_gap: 10
    save_type: all
    shaft: motor_servo_standard_01
    split: true
    split_z: 0.5
    typ: all
    type: default_bearing_plate
    width: 5
  link_github: https://github.com/oomlout/oomlout_oomp_version_1_messy/tree/main/parts/oobb_part_plate_bearing_6709_bearing_size_5_width_5_height_12_depth_motor_servo_standard_01_h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
  link_main: https://github.com/oomlout/oomlout_oomp_version_1_messy/tree/main/parts/oobb_part_plate_bearing_6709_bearing_size_5_width_5_height_12_depth_motor_servo_standard_01_h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
  link_redirect: https://github.com/oomlout/oomlout_oomp_version_1_messy/tree/main/parts/oobb_part_plate_bearing_6709_bearing_size_5_width_5_height_12_depth_motor_servo_standard_01_h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
  manufacturer: ''
  md5: c7855dafcd60b78f2626712a17fdce44
  md5_10: c7855dafcd
  md5_10_upper: C7855DAFCD
  md5_5: c7855
  md5_5_upper: C7855
  md5_6: c7855d
  md5_6_alpha: 7s9ct
  md5_6_alpha_upper: 7S9CT
  md5_6_upper: C7855D
  name: Oobb Part Plate Bearing 6709 Bearing Size 5 Width 5 Height 12 Depth Motor
    Servo Standard 01 Horn Adapter Screws
  name_no_class: Oobb Part Plate Bearing 6709 Bearing Size 5 Width 5 Height 12 Depth
    Motor Servo Standard 01 Horn Adapter Screws
  name_no_size: Oobb Part Plate Bearing 6709 Bearing Size 5 Width 5 Height 12 Depth
    Motor Servo Standard 01 Horn Adapter Screws
  name_no_type: Oobb Part Plate Bearing 6709 Bearing Size 5 Width 5 Height 12 Depth
    Motor Servo Standard 01 Horn Adapter Screws
  name_proper: Oobb Part Plate Bearing 6709 Bearing Size 5 Width 5 Height 12 Depth
    Motor Servo Standard 01 Horn Adapter Screws
  name_short: Default Bearing Plate 5x5xMotor Servo
  name_space: oobb part plate bearing 6709 bearing size 5 width 5 height 12 depth
    motor servo standard 01 horn adapter screws
  name_text: Oobb Part Default Bearing Plate 5 Width 5 Height Motor Servo Standard
    01 Shaft Motor Servo Standard 01 Horn Adapter Screws Extra 12 Depth
  name_upper: OOBB PART PLATE BEARING 6709 BEARING SIZE 5 WIDTH 5 HEIGHT 12 DEPTH
    MOTOR SERVO STANDARD 01 HORN ADAPTER SCREWS
  oobb_details:
    bearing_depth: 6
    bearing_inner_diameter: 45
    bearing_outer_diameter: 55
    bearing_print_radial_clearance: 0.2
    bearing_size: '6709'
    body: cylinder
    depth: 12
    extra: motor_servo_standard_01_horn_adapter_screws
    height: 5
    horn_adapter: screws
    inner_joining_rotation: 45
    interior_grid: 0
    interior_hole_positions: []
    interior_radius_name: m3
    joining_tangent_clearance: 0.01
    oobb_name: bearing_plate
    prepare_print: true
    print_gap: 10
    shaft: motor_servo_standard_01
    split: true
    split_z: 0.5
    width: 5
  oobb_name: bearing_plate
  oomlout_ai_roboclick_1:
    actions:
    - command: text_jinja_template
      convert_to_pdf: false
      convert_to_png: false
      dict_data:
        bearing_depth: 6
        bearing_dimension_source: https://www.cxnjs.com/content/150.html
        bearing_inner_diameter: 45
        bearing_outer_diameter: 55
        bearing_print_radial_clearance: 0.2
        bearing_size: '6709'
        body: cylinder
        depth: 12
        directory: parts\oobb_part_plate_bearing_6709_bearing_size_5_width_5_height_12_depth_motor_servo_standard_01_horn_adapter_screws
        extra: motor_servo_standard_01_horn_adapter_screws
        height: 5
        horn_adapter: screws
        id: oobb_part_plate_bearing_6709_bearing_size_5_width_5_height_12_depth_motor_servo_standard_01_horn_adapter_screws
        inner_joining_rotation: 45
        interior_grid: 0
        name: oobb_part_plate_bearing_6709_bearing_size_5_width_5_height_12_depth_motor_servo_standard_01_horn_adapter_screws
        name_proper: Oobb Part Plate Bearing 6709 Bearing Size 5 Width 5 Height 12
          Depth Motor Servo Standard 01 Horn Adapter Screws
        name_space: oobb part plate bearing 6709 bearing size 5 width 5 height 12
          depth motor servo standard 01 horn adapter screws
        name_upper: OOBB PART PLATE BEARING 6709 BEARING SIZE 5 WIDTH 5 HEIGHT 12
          DEPTH MOTOR SERVO STANDARD 01 HORN ADAPTER SCREWS
        oobb_details:
          bearing_depth: 6
          bearing_inner_diameter: 45
          bearing_outer_diameter: 55
          bearing_print_radial_clearance: 0.2
          bearing_size: '6709'
          body: cylinder
          depth: 12
          extra: motor_servo_standard_01_horn_adapter_screws
          height: 5
          horn_adapter: screws
          inner_joining_rotation: 45
          interior_grid: 0
          interior_hole_positions: []
          interior_radius_name: m3
          joining_tangent_clearance: 0.01
          oobb_name: bearing_plate
          prepare_print: true
          print_gap: 10
          shaft: motor_servo_standard_01
          split: true
          split_z: 0.5
          width: 5
        shaft: motor_servo_standard_01
        split_z: 0.5
        taxonomy_1: oobb
        taxonomy_10: ''
        taxonomy_11: ''
        taxonomy_12: ''
        taxonomy_13: ''
        taxonomy_14: ''
        taxonomy_15: ''
        taxonomy_2: part
        taxonomy_3: plate
        taxonomy_4: bearing
        taxonomy_5: 6709_bearing_size
        taxonomy_6: 5_width
        taxonomy_7: 5_height
        taxonomy_8: 12_depth
        taxonomy_9: motor_servo_standard_01_horn_adapter_screws
        url_chat: ''
        width: 5
      dict_data_files: {}
      dict_data_files_exists: {}
      file_output: label_oomp.svg
      file_template: C:\gh\oomlout_oobb_part_plate_bearing_version_5\source_file\template_jinja\template_jinja_label_oomlout_76_2_mm_50_8_mm\working.svg.j2
      search_and_replace: []
    file_test: label_oomp.pdf
    retries_until_complete: 0
  oomp_key: oomp_oobb_part_plate_bearing_6709_bearing_size_5_width_5_height_12_depth_motor_servo_standard_01_horn_adapter_screws
  part_number: ''
  shaft: motor_servo_standard_01
  short_name: ''
  size: default_bearing_plate
  split_z: 0.5
  taxonomy_1: oobb
  taxonomy_10: ''
  taxonomy_11: ''
  taxonomy_12: ''
  taxonomy_13: ''
  taxonomy_14: ''
  taxonomy_15: ''
  taxonomy_1_capital: Oobb
  taxonomy_1_first_letter: o
  taxonomy_1_first_letter_upper: O
  taxonomy_1_length_1: o
  taxonomy_1_length_2: oo
  taxonomy_1_length_3: oob
  taxonomy_1_length_4: oobb
  taxonomy_1_length_5: oobb
  taxonomy_1_upper: OOBB
  taxonomy_1_upper_length_1: O
  taxonomy_1_upper_length_2: OO
  taxonomy_1_upper_length_3: OOB
  taxonomy_1_upper_length_4: OOBB
  taxonomy_1_upper_length_5: OOBB
  taxonomy_2: part
  taxonomy_2_capital: Part
  taxonomy_2_first_letter: p
  taxonomy_2_first_letter_upper: P
  taxonomy_2_length_1: p
  taxonomy_2_length_2: pa
  taxonomy_2_length_3: par
  taxonomy_2_length_4: part
  taxonomy_2_length_5: part
  taxonomy_2_upper: PART
  taxonomy_2_upper_length_1: P
  taxonomy_2_upper_length_2: PA
  taxonomy_2_upper_length_3: PAR
  taxonomy_2_upper_length_4: PART
  taxonomy_2_upper_length_5: PART
  taxonomy_3: plate
  taxonomy_3_capital: Plate
  taxonomy_3_first_letter: p
  taxonomy_3_first_letter_upper: P
  taxonomy_3_length_1: p
  taxonomy_3_length_2: pl
  taxonomy_3_length_3: pla
  taxonomy_3_length_4: plat
  taxonomy_3_length_5: plate
  taxonomy_3_upper: PLATE
  taxonomy_3_upper_length_1: P
  taxonomy_3_upper_length_2: PL
  taxonomy_3_upper_length_3: PLA
  taxonomy_3_upper_length_4: PLAT
  taxonomy_3_upper_length_5: PLATE
  taxonomy_4: bearing
  taxonomy_4_capital: Bearing
  taxonomy_4_first_letter: b
  taxonomy_4_first_letter_upper: B
  taxonomy_4_length_1: b
  taxonomy_4_length_2: be
  taxonomy_4_length_3: bea
  taxonomy_4_length_4: bear
  taxonomy_4_length_5: beari
  taxonomy_4_upper: BEARING
  taxonomy_4_upper_length_1: B
  taxonomy_4_upper_length_2: BE
  taxonomy_4_upper_length_3: BEA
  taxonomy_4_upper_length_4: BEAR
  taxonomy_4_upper_length_5: BEARI
  taxonomy_5: 6709_bearing_size
  taxonomy_5_capital: 6709 Bearing Size
  taxonomy_5_first_letter: '6'
  taxonomy_5_first_letter_upper: '6'
  taxonomy_5_length_1: '6'
  taxonomy_5_length_2: '67'
  taxonomy_5_length_3: '670'
  taxonomy_5_length_4: '6709'
  taxonomy_5_length_5: '6709_'
  taxonomy_5_upper: 6709_BEARING_SIZE
  taxonomy_5_upper_length_1: '6'
  taxonomy_5_upper_length_2: '67'
  taxonomy_5_upper_length_3: '670'
  taxonomy_5_upper_length_4: '6709'
  taxonomy_5_upper_length_5: '6709_'
  taxonomy_6: 5_width
  taxonomy_6_capital: 5 Width
  taxonomy_6_first_letter: '5'
  taxonomy_6_first_letter_upper: '5'
  taxonomy_6_length_1: '5'
  taxonomy_6_length_2: '5_'
  taxonomy_6_length_3: 5_w
  taxonomy_6_length_4: 5_wi
  taxonomy_6_length_5: 5_wid
  taxonomy_6_upper: 5_WIDTH
  taxonomy_6_upper_length_1: '5'
  taxonomy_6_upper_length_2: '5_'
  taxonomy_6_upper_length_3: 5_W
  taxonomy_6_upper_length_4: 5_WI
  taxonomy_6_upper_length_5: 5_WID
  taxonomy_7: 5_height
  taxonomy_7_capital: 5 Height
  taxonomy_7_first_letter: '5'
  taxonomy_7_first_letter_upper: '5'
  taxonomy_7_length_1: '5'
  taxonomy_7_length_2: '5_'
  taxonomy_7_length_3: 5_h
  taxonomy_7_length_4: 5_he
  taxonomy_7_length_5: 5_hei
  taxonomy_7_upper: 5_HEIGHT
  taxonomy_7_upper_length_1: '5'
  taxonomy_7_upper_length_2: '5_'
  taxonomy_7_upper_length_3: 5_H
  taxonomy_7_upper_length_4: 5_HE
  taxonomy_7_upper_length_5: 5_HEI
  taxonomy_8: 12_depth
  taxonomy_8_capital: 12 Depth
  taxonomy_8_first_letter: '1'
  taxonomy_8_first_letter_upper: '1'
  taxonomy_8_length_1: '1'
  taxonomy_8_length_2: '12'
  taxonomy_8_length_3: '12_'
  taxonomy_8_length_4: 12_d
  taxonomy_8_length_5: 12_de
  taxonomy_8_upper: 12_DEPTH
  taxonomy_8_upper_length_1: '1'
  taxonomy_8_upper_length_2: '12'
  taxonomy_8_upper_length_3: '12_'
  taxonomy_8_upper_length_4: 12_D
  taxonomy_8_upper_length_5: 12_DE
  taxonomy_9: motor_servo_standard_01_horn_adapter_screws
  taxonomy_9_capital: Motor Servo Standard 01 Horn Adapter Screws
  taxonomy_9_first_letter: m
  taxonomy_9_first_letter_upper: M
  taxonomy_9_length_1: m
  taxonomy_9_length_2: mo
  taxonomy_9_length_3: mot
  taxonomy_9_length_4: moto
  taxonomy_9_length_5: motor
  taxonomy_9_upper: MOTOR_SERVO_STANDARD_01_HORN_ADAPTER_SCREWS
  taxonomy_9_upper_length_1: M
  taxonomy_9_upper_length_2: MO
  taxonomy_9_upper_length_3: MOT
  taxonomy_9_upper_length_4: MOTO
  taxonomy_9_upper_length_5: MOTOR
  type: part
  url_chat: ''
  width: 5
  width_mm: 74
url_chat: ''
width: 5
