oomlout/oomlout_oobb_part_holder_bearing_version_5/navigation_oobb/oobb/part/plate/bearing/6810_bearing_size/7_width/5_height/12_depth/inside_embedded_m3_nuts/thing.yaml

bearing_size: '6810'
bip_39_2_word_array:
- road
- link
bip_39_2_word_no_space: roadlink
bip_39_2_word_space: road link
bip_39_2_word_underscore: road_link
bip_39_3_word_array:
- road
- link
- situate
bip_39_3_word_no_space: roadlinksituate
bip_39_3_word_space: road link situate
bip_39_3_word_underscore: road_link_situate
bip_39_full_array:
- road
- link
- situate
- rude
- marriage
- spend
- simple
- timber
- million
- blanket
- bind
- stairs
bip_39_full_no_space: roadlinksituaterudemarriagespendsimpletimbermillionblanketbindstairs
bip_39_full_space: road link situate rude marriage spend simple timber million blanket
  bind stairs
bip_39_full_underscore: road_link_situate_rude_marriage_spend_simple_timber_million_blanket_bind_stairs
depth: 12
directory: parts/oobb_part_plate_bearing_6810_bearing_size_7_width_5_height_12_depth_inside_embedded_m3_nuts
embedded_nut_positions: &id001
- - -15
  - 0
- - 15
  - 0
- - 0
  - -15
- - 0
  - 15
- - -15
  - -15
- - -15
  - 15
- - 15
  - -15
- - 15
  - 15
embedded_nut_radius_name: m3
embedded_nut_rotation: 30
embedded_nut_rotation_radial: true
extra: inside_embedded_m3_nuts
height: 5
id: oobb_part_plate_bearing_6810_bearing_size_7_width_5_height_12_depth_inside_embedded_m3_nuts
id_no_class: oobb_part_plate_bearing_6810_bearing_size_7_width_5_height_12_depth_inside_embedded_m3_nuts
id_no_size: oobb_part_plate_bearing_6810_bearing_size_7_width_5_height_12_depth_inside_embedded_m3_nuts
id_no_type: oobb_part_plate_bearing_6810_bearing_size_7_width_5_height_12_depth_inside_embedded_m3_nuts
id_oobb: oobb_part_plate_bearing_6810_bearing_size_7_width_5_height_12_depth_inside_embedded_m3_nuts
inner_joining_rotation: 45
inside: embedded_m3_nuts
interior_grid: 0
kwargs:
  bearing_size: '6810'
  body: plate
  depth: 12
  embedded_nut_positions:
  - - -15
    - 0
  - - 15
    - 0
  - - 0
    - -15
  - - 0
    - 15
  - - -15
    - -15
  - - -15
    - 15
  - - 15
    - -15
  - - 15
    - 15
  embedded_nut_radius_name: m3
  embedded_nut_rotation: 30
  embedded_nut_rotation_radial: true
  extra: inside_embedded_m3_nuts
  filter: ''
  height: 5
  horn_adapter: ''
  inner_joining_rotation: 45
  inside: embedded_m3_nuts
  interior_grid: 0
  interior_hole_positions: []
  interior_radius_name: m3
  joining_tangent_clearance: 0.01
  modes:
  - 3dpr
  navigation: true
  oobb_name: bearing_plate
  oomp_description_extra: m6_shaft_inside_embedded_m3_nuts_extra_12_depth
  oomp_description_main: bearing_plate_7_width_5_height
  oomp_mode: project
  oomp_run: true
  overwrite: true
  prepare_print: true
  print_gap: 10
  shaft: m6
  split: true
  split_z: 0
  typ: all
  type: default_bearing_plate
  width: 7
link_github: https://github.com/oomlout/oomlout_oomp_version_1_messy/tree/main/parts/oobb_part_plate_bearing_6810_bearing_size_7_width_5_height_12_depth_inside_embedded_m3_nuts
link_main: https://github.com/oomlout/oomlout_oomp_version_1_messy/tree/main/parts/oobb_part_plate_bearing_6810_bearing_size_7_width_5_height_12_depth_inside_embedded_m3_nuts
link_redirect: https://github.com/oomlout/oomlout_oomp_version_1_messy/tree/main/parts/oobb_part_plate_bearing_6810_bearing_size_7_width_5_height_12_depth_inside_embedded_m3_nuts
md5: baf04326de7885a2b247118ca2e8596a
md5_10: baf04326de
md5_10_upper: BAF04326DE
md5_5: baf04
md5_5_upper: BAF04
md5_6: baf043
md5_6_alpha: 7al37
md5_6_alpha_upper: 7AL37
md5_6_upper: BAF043
name: Oobb Part Plate Bearing 6810 Bearing Size 7 Width 5 Height 12 Depth Inside Embedded
  M3 Nuts
name_no_class: Oobb Part Plate Bearing 6810 Bearing Size 7 Width 5 Height 12 Depth
  Inside Embedded M3 Nuts
name_no_size: Oobb Part Plate Bearing 6810 Bearing Size 7 Width 5 Height 12 Depth
  Inside Embedded M3 Nuts
name_no_type: Oobb Part Plate Bearing 6810 Bearing Size 7 Width 5 Height 12 Depth
  Inside Embedded M3 Nuts
name_proper: Oobb Part Plate Bearing 6810 Bearing Size 7 Width 5 Height 12 Depth Inside
  Embedded M3 Nuts
name_space: oobb part plate bearing 6810 bearing size 7 width 5 height 12 depth inside
  embedded m3 nuts
name_upper: OOBB PART PLATE BEARING 6810 BEARING SIZE 7 WIDTH 5 HEIGHT 12 DEPTH INSIDE
  EMBEDDED M3 NUTS
oobb_details:
  bearing_size: '6810'
  body: plate
  depth: 12
  embedded_nut_positions: *id001
  embedded_nut_radius_name: m3
  embedded_nut_rotation: 30
  embedded_nut_rotation_radial: true
  extra: inside_embedded_m3_nuts
  height: 5
  horn_adapter: ''
  inner_joining_rotation: 45
  inside: embedded_m3_nuts
  interior_grid: 0
  interior_hole_positions: []
  interior_radius_name: m3
  joining_tangent_clearance: 0.01
  oobb_name: bearing_plate
  prepare_print: true
  print_gap: 10
  shaft: m6
  split: true
  split_z: 0
  width: 7
oobb_name: bearing_plate
oomlout_ai_roboclick_1:
  actions:
  - command: text_jinja_template
    convert_to_pdf: false
    convert_to_png: false
    dict_data:
      bearing_size: '6810'
      depth: 12
      directory: parts\oobb_part_plate_bearing_6810_bearing_size_7_width_5_height_12_depth_inside_embedded_m3_nuts
      embedded_nut_positions: &id002
      - - -15
        - 0
      - - 15
        - 0
      - - 0
        - -15
      - - 0
        - 15
      - - -15
        - -15
      - - -15
        - 15
      - - 15
        - -15
      - - 15
        - 15
      embedded_nut_radius_name: m3
      embedded_nut_rotation: 30
      embedded_nut_rotation_radial: true
      extra: inside_embedded_m3_nuts
      height: 5
      id: oobb_part_plate_bearing_6810_bearing_size_7_width_5_height_12_depth_inside_embedded_m3_nuts
      inner_joining_rotation: 45
      inside: embedded_m3_nuts
      interior_grid: 0
      name: oobb_part_plate_bearing_6810_bearing_size_7_width_5_height_12_depth_inside_embedded_m3_nuts
      name_proper: Oobb Part Plate Bearing 6810 Bearing Size 7 Width 5 Height 12 Depth
        Inside Embedded M3 Nuts
      name_space: oobb part plate bearing 6810 bearing size 7 width 5 height 12 depth
        inside embedded m3 nuts
      name_upper: OOBB PART PLATE BEARING 6810 BEARING SIZE 7 WIDTH 5 HEIGHT 12 DEPTH
        INSIDE EMBEDDED M3 NUTS
      oobb_details:
        bearing_size: '6810'
        body: plate
        depth: 12
        embedded_nut_positions: *id002
        embedded_nut_radius_name: m3
        embedded_nut_rotation: 30
        embedded_nut_rotation_radial: true
        extra: inside_embedded_m3_nuts
        height: 5
        horn_adapter: ''
        inner_joining_rotation: 45
        inside: embedded_m3_nuts
        interior_grid: 0
        interior_hole_positions: []
        interior_radius_name: m3
        joining_tangent_clearance: 0.01
        oobb_name: bearing_plate
        prepare_print: true
        print_gap: 10
        shaft: m6
        split: true
        split_z: 0
        width: 7
      taxonomy_1: oobb
      taxonomy_10: ''
      taxonomy_11: ''
      taxonomy_12: ''
      taxonomy_13: ''
      taxonomy_14: ''
      taxonomy_15: ''
      taxonomy_2: part
      taxonomy_3: plate
      taxonomy_4: bearing
      taxonomy_5: 6810_bearing_size
      taxonomy_6: 7_width
      taxonomy_7: 5_height
      taxonomy_8: 12_depth
      taxonomy_9: inside_embedded_m3_nuts
      url_chat: ''
      width: 7
    dict_data_files: {}
    dict_data_files_exists: {}
    file_output: label_oomp.svg
    file_template: C:\gh\oomlout_oobb_part_plate_bearing_version_5\source_file\template_jinja\template_jinja_label_oomlout_76_2_mm_50_8_mm\working.svg.j2
    search_and_replace: []
  file_test: label_oomp.pdf
  retries_until_complete: 0
oomp_key: oomp_oobb_part_plate_bearing_6810_bearing_size_7_width_5_height_12_depth_inside_embedded_m3_nuts
project_name: C:\gh\oomlout_oobb_part_plate_bearing_version_5
taxonomy_1: oobb
taxonomy_10: ''
taxonomy_11: ''
taxonomy_12: ''
taxonomy_13: ''
taxonomy_14: ''
taxonomy_15: ''
taxonomy_1_capital: Oobb
taxonomy_1_first_letter: o
taxonomy_1_first_letter_upper: O
taxonomy_1_length_1: o
taxonomy_1_length_2: oo
taxonomy_1_length_3: oob
taxonomy_1_length_4: oobb
taxonomy_1_length_5: oobb
taxonomy_1_upper: OOBB
taxonomy_1_upper_length_1: O
taxonomy_1_upper_length_2: OO
taxonomy_1_upper_length_3: OOB
taxonomy_1_upper_length_4: OOBB
taxonomy_1_upper_length_5: OOBB
taxonomy_2: part
taxonomy_2_capital: Part
taxonomy_2_first_letter: p
taxonomy_2_first_letter_upper: P
taxonomy_2_length_1: p
taxonomy_2_length_2: pa
taxonomy_2_length_3: par
taxonomy_2_length_4: part
taxonomy_2_length_5: part
taxonomy_2_upper: PART
taxonomy_2_upper_length_1: P
taxonomy_2_upper_length_2: PA
taxonomy_2_upper_length_3: PAR
taxonomy_2_upper_length_4: PART
taxonomy_2_upper_length_5: PART
taxonomy_3: plate
taxonomy_3_capital: Plate
taxonomy_3_first_letter: p
taxonomy_3_first_letter_upper: P
taxonomy_3_length_1: p
taxonomy_3_length_2: pl
taxonomy_3_length_3: pla
taxonomy_3_length_4: plat
taxonomy_3_length_5: plate
taxonomy_3_upper: PLATE
taxonomy_3_upper_length_1: P
taxonomy_3_upper_length_2: PL
taxonomy_3_upper_length_3: PLA
taxonomy_3_upper_length_4: PLAT
taxonomy_3_upper_length_5: PLATE
taxonomy_4: bearing
taxonomy_4_capital: Bearing
taxonomy_4_first_letter: b
taxonomy_4_first_letter_upper: B
taxonomy_4_length_1: b
taxonomy_4_length_2: be
taxonomy_4_length_3: bea
taxonomy_4_length_4: bear
taxonomy_4_length_5: beari
taxonomy_4_upper: BEARING
taxonomy_4_upper_length_1: B
taxonomy_4_upper_length_2: BE
taxonomy_4_upper_length_3: BEA
taxonomy_4_upper_length_4: BEAR
taxonomy_4_upper_length_5: BEARI
taxonomy_5: 6810_bearing_size
taxonomy_5_capital: 6810 Bearing Size
taxonomy_5_first_letter: '6'
taxonomy_5_first_letter_upper: '6'
taxonomy_5_length_1: '6'
taxonomy_5_length_2: '68'
taxonomy_5_length_3: '681'
taxonomy_5_length_4: '6810'
taxonomy_5_length_5: '6810_'
taxonomy_5_upper: 6810_BEARING_SIZE
taxonomy_5_upper_length_1: '6'
taxonomy_5_upper_length_2: '68'
taxonomy_5_upper_length_3: '681'
taxonomy_5_upper_length_4: '6810'
taxonomy_5_upper_length_5: '6810_'
taxonomy_6: 7_width
taxonomy_6_capital: 7 Width
taxonomy_6_first_letter: '7'
taxonomy_6_first_letter_upper: '7'
taxonomy_6_length_1: '7'
taxonomy_6_length_2: '7_'
taxonomy_6_length_3: 7_w
taxonomy_6_length_4: 7_wi
taxonomy_6_length_5: 7_wid
taxonomy_6_upper: 7_WIDTH
taxonomy_6_upper_length_1: '7'
taxonomy_6_upper_length_2: '7_'
taxonomy_6_upper_length_3: 7_W
taxonomy_6_upper_length_4: 7_WI
taxonomy_6_upper_length_5: 7_WID
taxonomy_7: 5_height
taxonomy_7_capital: 5 Height
taxonomy_7_first_letter: '5'
taxonomy_7_first_letter_upper: '5'
taxonomy_7_length_1: '5'
taxonomy_7_length_2: '5_'
taxonomy_7_length_3: 5_h
taxonomy_7_length_4: 5_he
taxonomy_7_length_5: 5_hei
taxonomy_7_upper: 5_HEIGHT
taxonomy_7_upper_length_1: '5'
taxonomy_7_upper_length_2: '5_'
taxonomy_7_upper_length_3: 5_H
taxonomy_7_upper_length_4: 5_HE
taxonomy_7_upper_length_5: 5_HEI
taxonomy_8: 12_depth
taxonomy_8_capital: 12 Depth
taxonomy_8_first_letter: '1'
taxonomy_8_first_letter_upper: '1'
taxonomy_8_length_1: '1'
taxonomy_8_length_2: '12'
taxonomy_8_length_3: '12_'
taxonomy_8_length_4: 12_d
taxonomy_8_length_5: 12_de
taxonomy_8_upper: 12_DEPTH
taxonomy_8_upper_length_1: '1'
taxonomy_8_upper_length_2: '12'
taxonomy_8_upper_length_3: '12_'
taxonomy_8_upper_length_4: 12_D
taxonomy_8_upper_length_5: 12_DE
taxonomy_9: inside_embedded_m3_nuts
taxonomy_9_capital: Inside Embedded M3 Nuts
taxonomy_9_first_letter: i
taxonomy_9_first_letter_upper: I
taxonomy_9_length_1: i
taxonomy_9_length_2: in
taxonomy_9_length_3: ins
taxonomy_9_length_4: insi
taxonomy_9_length_5: insid
taxonomy_9_upper: INSIDE_EMBEDDED_M3_NUTS
taxonomy_9_upper_length_1: I
taxonomy_9_upper_length_2: IN
taxonomy_9_upper_length_3: INS
taxonomy_9_upper_length_4: INSI
taxonomy_9_upper_length_5: INSID
thing:
  bearing_size: '6810'
  bip_39_2_word_array:
  - road
  - link
  bip_39_2_word_no_space: roadlink
  bip_39_2_word_space: road link
  bip_39_2_word_underscore: road_link
  bip_39_3_word_array:
  - road
  - link
  - situate
  bip_39_3_word_no_space: roadlinksituate
  bip_39_3_word_space: road link situate
  bip_39_3_word_underscore: road_link_situate
  bip_39_full_array:
  - road
  - link
  - situate
  - rude
  - marriage
  - spend
  - simple
  - timber
  - million
  - blanket
  - bind
  - stairs
  bip_39_full_no_space: roadlinksituaterudemarriagespendsimpletimbermillionblanketbindstairs
  bip_39_full_space: road link situate rude marriage spend simple timber million blanket
    bind stairs
  bip_39_full_underscore: road_link_situate_rude_marriage_spend_simple_timber_million_blanket_bind_stairs
  classification: oobb
  color: ''
  components:
  - inclusion: 3dpr
    objects:
    - inclusion: 3dpr
      objects:
      - - depth: 12
          height: 5
          inclusion: 3dpr
          pos:
          - 0
          - 0
          - -6.0
          shape: rounded_rectangle
          size:
          - 105.0
          - 75.0
          - 12
          type: positive
          width: 7
      - inclusion: 3dpr
        objects:
        - - depth: 7
            h: 7
            inclusion: laser
            pos: &id003
            - 0
            - 0
            - -3.5
            r: 32.7
            shape: cylinder
            type: positive
          - depth: 7
            h: 7
            inclusion: 3dpr
            pos: *id003
            r: 32.7
            shape: cylinder
            type: positive
          - depth: 7
            h: 7
            inclusion: 'true'
            pos: *id003
            r: 32.7
            shape: cylinder
            type: positive
        - - depth: 7.02
            h: 7.02
            inclusion: laser
            pos: &id004
            - 0
            - 0
            - -3.51
            r: 25
            shape: cylinder
            type: negative
          - depth: 7.02
            h: 7.02
            inclusion: 3dpr
            pos: *id004
            r: 25
            shape: cylinder
            type: negative
          - depth: 7.02
            h: 7.02
            inclusion: 'true'
            pos: *id004
            r: 25
            shape: cylinder
            type: negative
        pos:
        - 0
        - 0
        - 0
        rot:
        - 0
        - 0
        - 0
        type: rotation
        typetype: negative
      - inclusion: 3dpr
        objects:
        - - depth: 42
            h: 42
            inclusion: laser
            pos: &id005
            - 0
            - 0
            - -21.0
            r: 29.35
            shape: cylinder
            type: positive
          - depth: 42
            h: 42
            inclusion: 3dpr
            pos: *id005
            r: 29.35
            shape: cylinder
            type: positive
          - depth: 42
            h: 42
            inclusion: 'true'
            pos: *id005
            r: 29.35
            shape: cylinder
            type: positive
        - - depth: 42.02
            h: 42.02
            inclusion: laser
            pos: &id006
            - 0
            - 0
            - -21.01
            r: 28.35
            shape: cylinder
            type: negative
          - depth: 42.02
            h: 42.02
            inclusion: 3dpr
            pos: *id006
            r: 28.35
            shape: cylinder
            type: negative
          - depth: 42.02
            h: 42.02
            inclusion: 'true'
            pos: *id006
            r: 28.35
            shape: cylinder
            type: negative
        pos:
        - 0
        - 0
        - 0
        rot:
        - 0
        - 0
        - 0
        type: rotation
        typetype: negative
      - - - depth: 14
            h: 14
            inclusion: laser
            m: ''
            pos:
            - -45.0
            - -30.0
            - -7.0
            r: 3.0
            shape: cylinder
            type: negative
          - depth: 14
            h: 14
            inclusion: 3dpr
            m: ''
            pos:
            - -45.0
            - -30.0
            - -7.0
            r: 3.25
            shape: cylinder
            type: negative
          - depth: 14
            h: 14
            inclusion: 'true'
            m: ''
            pos:
            - -45.0
            - -30.0
            - -7.0
            r: 3.0
            shape: cylinder
            type: negative
        - - depth: 14
            h: 14
            inclusion: laser
            m: ''
            pos:
            - -45.0
            - -15.0
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
  - oobb_holes_shape_negative_type_m6_radius_name_14_depth_0_0_-7.0_pos_7_width_5_height_'top'_'bottom'_holes_3dpr_mode
  - oobb_holes_shape_negative_type_m6_radius_name_14_depth_0_0_-7.0_pos_5_width_5_height_corners_holes_3dpr_mode
  - oobb_nut_shape_negative_type_m3_radius_name_3_depth_-15_0_0_pos_middle_zz_0_0_210.0_rot_false_overhang_3dpr_mode
  - oobb_hole_shape_negative_type_m3_radius_name_14_depth_-15_0_-7.0_pos_3dpr_mode
  - oobb_nut_shape_negative_type_m3_radius_name_3_depth_15_0_0_pos_middle_zz_0_0_30.0_rot_false_overhang_3dpr_mode
  - oobb_hole_shape_negative_type_m3_radius_name_14_depth_15_0_-7.0_pos_3dpr_mode
  - oobb_nut_shape_negative_type_m3_radius_name_3_depth_0_-15_0_pos_middle_zz_0_0_-60.0_rot_false_overhang_3dpr_mode
  - oobb_hole_shape_negative_type_m3_radius_name_14_depth_0_-15_-7.0_pos_3dpr_mode
  - oobb_nut_shape_negative_type_m3_radius_name_3_depth_0_15_0_pos_middle_zz_0_0_120.0_rot_false_overhang_3dpr_mode
  - oobb_hole_shape_negative_type_m3_radius_name_14_depth_0_15_-7.0_pos_3dpr_mode
  - oobb_nut_shape_negative_type_m3_radius_name_3_depth_-15_-15_0_pos_middle_zz_0_0_-105.0_rot_false_overhang_3dpr_mode
  - oobb_hole_shape_negative_type_m3_radius_name_14_depth_-15_-15_-7.0_pos_3dpr_mode
  - oobb_nut_shape_negative_type_m3_radius_name_3_depth_-15_15_0_pos_middle_zz_0_0_165.0_rot_false_overhang_3dpr_mode
  - oobb_hole_shape_negative_type_m3_radius_name_14_depth_-15_15_-7.0_pos_3dpr_mode
  - oobb_nut_shape_negative_type_m3_radius_name_3_depth_15_-15_0_pos_middle_zz_0_0_-15.0_rot_false_overhang_3dpr_mode
  - oobb_hole_shape_negative_type_m3_radius_name_14_depth_15_-15_-7.0_pos_3dpr_mode
  - oobb_nut_shape_negative_type_m3_radius_name_3_depth_15_15_0_pos_middle_zz_0_0_75.0_rot_false_overhang_3dpr_mode
  - oobb_hole_shape_negative_type_m3_radius_name_14_depth_15_15_-7.0_pos_3dpr_mode
  - oobb_screw_countersunk_shape_negative_type_m3_radius_name_12_depth_30.0_-22_6.0_pos_0_0_0_rot_0_0_30_rotation_nut_true_hole_true_nut_include_true_overhang_3dpr_mode
  - oobb_screw_countersunk_shape_negative_type_m3_radius_name_12_depth_-22_-30.0_-6.0_pos_0_180_0_rot_0_0_0_rotation_nut_true_hole_true_nut_include_true_overhang_3dpr_mode
  - oobb_screw_countersunk_shape_negative_type_m3_radius_name_12_depth_-30.0_22_6.0_pos_0_0_0_rot_0_0_30_rotation_nut_true_hole_true_nut_include_true_overhang_3dpr_mode
  - oobb_screw_countersunk_shape_negative_type_m3_radius_name_12_depth_22_30.0_-6.0_pos_0_180_0_rot_0_0_0_rotation_nut_true_hole_true_nut_include_true_overhang_3dpr_mode
  - oobb_screw_countersunk_shape_negative_type_m3_radius_name_12_depth_-10.606601717798213_10.606601717798213_6.0_pos_0_0_0_rot_0_0_45.0_rotation_nut_true_hole_true_nut_include_true_overhang_3dpr_mode
  - oobb_screw_countersunk_shape_negative_type_m3_radius_name_12_depth_10.606601717798213_-10.606601717798213_-6.0_pos_0_180_0_rot_0_0_45.0_rotation_nut_true_hole_true_nut_include_true_overhang_3dpr_mode
  - oobb_hole_shape_negative_type_m6_radius_name_14_depth_0_0_-7.0_pos_3dpr_mode
  depth: 12
  description: default bearing plate 7x5x0
  description_extra: m6_shaft_inside_embedded_m3_nuts_extra_12_depth
  description_main: 7_width_5_height
  directory: parts/oobb_part_plate_bearing_6810_bearing_size_7_width_5_height_12_depth_inside_embedded_m3_nuts
  embedded_nut_positions: &id011
  - - -15
    - 0
  - - 15
    - 0
  - - 0
    - -15
  - - 0
    - 15
  - - -15
    - -15
  - - -15
    - 15
  - - 15
    - -15
  - - 15
    - 15
  embedded_nut_radius_name: m3
  embedded_nut_rotation: 30
  embedded_nut_rotation_radial: true
  extra: inside_embedded_m3_nuts
  height: 5
  height_mm: 74
  id: oobb_part_plate_bearing_6810_bearing_size_7_width_5_height_12_depth_inside_embedded_m3_nuts
  id_no_class: oobb_part_plate_bearing_6810_bearing_size_7_width_5_height_12_depth_inside_embedded_m3_nuts
  id_no_size: oobb_part_plate_bearing_6810_bearing_size_7_width_5_height_12_depth_inside_embedded_m3_nuts
  id_no_type: oobb_part_plate_bearing_6810_bearing_size_7_width_5_height_12_depth_inside_embedded_m3_nuts
  inner_joining_rotation: 45
  inside: embedded_m3_nuts
  interior_grid: 0
  kwargs:
    bearing_size: '6810'
    body: plate
    depth: 12
    embedded_nut_positions:
    - - -15
      - 0
    - - 15
      - 0
    - - 0
      - -15
    - - 0
      - 15
    - - -15
      - -15
    - - -15
      - 15
    - - 15
      - -15
    - - 15
      - 15
    embedded_nut_radius_name: m3
    embedded_nut_rotation: 30
    embedded_nut_rotation_radial: true
    extra: inside_embedded_m3_nuts
    filter: ''
    height: 5
    horn_adapter: ''
    inner_joining_rotation: 45
    inside: embedded_m3_nuts
    interior_grid: 0
    interior_hole_positions: []
    interior_radius_name: m3
    joining_tangent_clearance: 0.01
    modes:
    - 3dpr
    navigation: true
    oobb_name: bearing_plate
    oomp_description_extra: m6_shaft_inside_embedded_m3_nuts_extra_12_depth
    oomp_description_main: bearing_plate_7_width_5_height
    oomp_mode: project
    oomp_run: true
    overwrite: true
    prepare_print: true
    print_gap: 10
    save_type: all
    shaft: m6
    split: true
    split_z: 0
    typ: all
    type: default_bearing_plate
    width: 7
  link_github: https://github.com/oomlout/oomlout_oomp_version_1_messy/tree/main/parts/oobb_part_plate_bearing_6810_bearing_size_7_width_5_height_12_depth_inside_embedded_m3_nuts
  link_main: https://github.com/oomlout/oomlout_oomp_version_1_messy/tree/main/parts/oobb_part_plate_bearing_6810_bearing_size_7_width_5_height_12_depth_inside_embedded_m3_nuts
  link_redirect: https://github.com/oomlout/oomlout_oomp_version_1_messy/tree/main/parts/oobb_part_plate_bearing_6810_bearing_size_7_width_5_height_12_depth_inside_embedded_m3_nuts
  manufacturer: ''
  md5: baf04326de7885a2b247118ca2e8596a
  md5_10: baf04326de
  md5_10_upper: BAF04326DE
  md5_5: baf04
  md5_5_upper: BAF04
  md5_6: baf043
  md5_6_alpha: 7al37
  md5_6_alpha_upper: 7AL37
  md5_6_upper: BAF043
  name: Oobb Part Plate Bearing 6810 Bearing Size 7 Width 5 Height 12 Depth Inside
    Embedded M3 Nuts
  name_no_class: Oobb Part Plate Bearing 6810 Bearing Size 7 Width 5 Height 12 Depth
    Inside Embedded M3 Nuts
  name_no_size: Oobb Part Plate Bearing 6810 Bearing Size 7 Width 5 Height 12 Depth
    Inside Embedded M3 Nuts
  name_no_type: Oobb Part Plate Bearing 6810 Bearing Size 7 Width 5 Height 12 Depth
    Inside Embedded M3 Nuts
  name_proper: Oobb Part Plate Bearing 6810 Bearing Size 7 Width 5 Height 12 Depth
    Inside Embedded M3 Nuts
  name_short: Default Bearing Plate 7x5xM6 Shaft
  name_space: oobb part plate bearing 6810 bearing size 7 width 5 height 12 depth
    inside embedded m3 nuts
  name_text: Oobb Part Default Bearing Plate 7 Width 5 Height M6 Shaft Inside Embedded
    M3 Nuts Extra 12 Depth
  name_upper: OOBB PART PLATE BEARING 6810 BEARING SIZE 7 WIDTH 5 HEIGHT 12 DEPTH
    INSIDE EMBEDDED M3 NUTS
  oobb_details:
    bearing_size: '6810'
    body: plate
    depth: 12
    embedded_nut_positions: *id011
    embedded_nut_radius_name: m3
    embedded_nut_rotation: 30
    embedded_nut_rotation_radial: true
    extra: inside_embedded_m3_nuts
    height: 5
    horn_adapter: ''
    inner_joining_rotation: 45
    inside: embedded_m3_nuts
    interior_grid: 0
    interior_hole_positions: []
    interior_radius_name: m3
    joining_tangent_clearance: 0.01
    oobb_name: bearing_plate
    prepare_print: true
    print_gap: 10
    shaft: m6
    split: true
    split_z: 0
    width: 7
  oobb_name: bearing_plate
  oomlout_ai_roboclick_1:
    actions:
    - command: text_jinja_template
      convert_to_pdf: false
      convert_to_png: false
      dict_data:
        bearing_size: '6810'
        depth: 12
        directory: parts\oobb_part_plate_bearing_6810_bearing_size_7_width_5_height_12_depth_inside_embedded_m3_nuts
        embedded_nut_positions: &id012
        - - -15
          - 0
        - - 15
          - 0
        - - 0
          - -15
        - - 0
          - 15
        - - -15
          - -15
        - - -15
          - 15
        - - 15
          - -15
        - - 15
          - 15
        embedded_nut_radius_name: m3
        embedded_nut_rotation: 30
        embedded_nut_rotation_radial: true
        extra: inside_embedded_m3_nuts
        height: 5
        id: oobb_part_plate_bearing_6810_bearing_size_7_width_5_height_12_depth_inside_embedded_m3_nuts
        inner_joining_rotation: 45
        inside: embedded_m3_nuts
        interior_grid: 0
        name: oobb_part_plate_bearing_6810_bearing_size_7_width_5_height_12_depth_inside_embedded_m3_nuts
        name_proper: Oobb Part Plate Bearing 6810 Bearing Size 7 Width 5 Height 12
          Depth Inside Embedded M3 Nuts
        name_space: oobb part plate bearing 6810 bearing size 7 width 5 height 12
          depth inside embedded m3 nuts
        name_upper: OOBB PART PLATE BEARING 6810 BEARING SIZE 7 WIDTH 5 HEIGHT 12
          DEPTH INSIDE EMBEDDED M3 NUTS
        oobb_details:
          bearing_size: '6810'
          body: plate
          depth: 12
          embedded_nut_positions: *id012
          embedded_nut_radius_name: m3
          embedded_nut_rotation: 30
          embedded_nut_rotation_radial: true
          extra: inside_embedded_m3_nuts
          height: 5
          horn_adapter: ''
          inner_joining_rotation: 45
          inside: embedded_m3_nuts
          interior_grid: 0
          interior_hole_positions: []
          interior_radius_name: m3
          joining_tangent_clearance: 0.01
          oobb_name: bearing_plate
          prepare_print: true
          print_gap: 10
          shaft: m6
          split: true
          split_z: 0
          width: 7
        taxonomy_1: oobb
        taxonomy_10: ''
        taxonomy_11: ''
        taxonomy_12: ''
        taxonomy_13: ''
        taxonomy_14: ''
        taxonomy_15: ''
        taxonomy_2: part
        taxonomy_3: plate
        taxonomy_4: bearing
        taxonomy_5: 6810_bearing_size
        taxonomy_6: 7_width
        taxonomy_7: 5_height
        taxonomy_8: 12_depth
        taxonomy_9: inside_embedded_m3_nuts
        url_chat: ''
        width: 7
      dict_data_files: {}
      dict_data_files_exists: {}
      file_output: label_oomp.svg
      file_template: C:\gh\oomlout_oobb_part_plate_bearing_version_5\source_file\template_jinja\template_jinja_label_oomlout_76_2_mm_50_8_mm\working.svg.j2
      search_and_replace: []
    file_test: label_oomp.pdf
    retries_until_complete: 0
  oomp_key: oomp_oobb_part_plate_bearing_6810_bearing_size_7_width_5_height_12_depth_inside_embedded_m3_nuts
  part_number: ''
  shaft: m6
  short_name: ''
  size: default_bearing_plate
  taxonomy_1: oobb
  taxonomy_10: ''
  taxonomy_11: ''
  taxonomy_12: ''
  taxonomy_13: ''
  taxonomy_14: ''
  taxonomy_15: ''
  taxonomy_1_capital: Oobb
  taxonomy_1_first_letter: o
  taxonomy_1_first_letter_upper: O
  taxonomy_1_length_1: o
  taxonomy_1_length_2: oo
  taxonomy_1_length_3: oob
  taxonomy_1_length_4: oobb
  taxonomy_1_length_5: oobb
  taxonomy_1_upper: OOBB
  taxonomy_1_upper_length_1: O
  taxonomy_1_upper_length_2: OO
  taxonomy_1_upper_length_3: OOB
  taxonomy_1_upper_length_4: OOBB
  taxonomy_1_upper_length_5: OOBB
  taxonomy_2: part
  taxonomy_2_capital: Part
  taxonomy_2_first_letter: p
  taxonomy_2_first_letter_upper: P
  taxonomy_2_length_1: p
  taxonomy_2_length_2: pa
  taxonomy_2_length_3: par
  taxonomy_2_length_4: part
  taxonomy_2_length_5: part
  taxonomy_2_upper: PART
  taxonomy_2_upper_length_1: P
  taxonomy_2_upper_length_2: PA
  taxonomy_2_upper_length_3: PAR
  taxonomy_2_upper_length_4: PART
  taxonomy_2_upper_length_5: PART
  taxonomy_3: plate
  taxonomy_3_capital: Plate
  taxonomy_3_first_letter: p
  taxonomy_3_first_letter_upper: P
  taxonomy_3_length_1: p
  taxonomy_3_length_2: pl
  taxonomy_3_length_3: pla
  taxonomy_3_length_4: plat
  taxonomy_3_length_5: plate
  taxonomy_3_upper: PLATE
  taxonomy_3_upper_length_1: P
  taxonomy_3_upper_length_2: PL
  taxonomy_3_upper_length_3: PLA
  taxonomy_3_upper_length_4: PLAT
  taxonomy_3_upper_length_5: PLATE
  taxonomy_4: bearing
  taxonomy_4_capital: Bearing
  taxonomy_4_first_letter: b
  taxonomy_4_first_letter_upper: B
  taxonomy_4_length_1: b
  taxonomy_4_length_2: be
  taxonomy_4_length_3: bea
  taxonomy_4_length_4: bear
  taxonomy_4_length_5: beari
  taxonomy_4_upper: BEARING
  taxonomy_4_upper_length_1: B
  taxonomy_4_upper_length_2: BE
  taxonomy_4_upper_length_3: BEA
  taxonomy_4_upper_length_4: BEAR
  taxonomy_4_upper_length_5: BEARI
  taxonomy_5: 6810_bearing_size
  taxonomy_5_capital: 6810 Bearing Size
  taxonomy_5_first_letter: '6'
  taxonomy_5_first_letter_upper: '6'
  taxonomy_5_length_1: '6'
  taxonomy_5_length_2: '68'
  taxonomy_5_length_3: '681'
  taxonomy_5_length_4: '6810'
  taxonomy_5_length_5: '6810_'
  taxonomy_5_upper: 6810_BEARING_SIZE
  taxonomy_5_upper_length_1: '6'
  taxonomy_5_upper_length_2: '68'
  taxonomy_5_upper_length_3: '681'
  taxonomy_5_upper_length_4: '6810'
  taxonomy_5_upper_length_5: '6810_'
  taxonomy_6: 7_width
  taxonomy_6_capital: 7 Width
  taxonomy_6_first_letter: '7'
  taxonomy_6_first_letter_upper: '7'
  taxonomy_6_length_1: '7'
  taxonomy_6_length_2: '7_'
  taxonomy_6_length_3: 7_w
  taxonomy_6_length_4: 7_wi
  taxonomy_6_length_5: 7_wid
  taxonomy_6_upper: 7_WIDTH
  taxonomy_6_upper_length_1: '7'
  taxonomy_6_upper_length_2: '7_'
  taxonomy_6_upper_length_3: 7_W
  taxonomy_6_upper_length_4: 7_WI
  taxonomy_6_upper_length_5: 7_WID
  taxonomy_7: 5_height
  taxonomy_7_capital: 5 Height
  taxonomy_7_first_letter: '5'
  taxonomy_7_first_letter_upper: '5'
  taxonomy_7_length_1: '5'
  taxonomy_7_length_2: '5_'
  taxonomy_7_length_3: 5_h
  taxonomy_7_length_4: 5_he
  taxonomy_7_length_5: 5_hei
  taxonomy_7_upper: 5_HEIGHT
  taxonomy_7_upper_length_1: '5'
  taxonomy_7_upper_length_2: '5_'
  taxonomy_7_upper_length_3: 5_H
  taxonomy_7_upper_length_4: 5_HE
  taxonomy_7_upper_length_5: 5_HEI
  taxonomy_8: 12_depth
  taxonomy_8_capital: 12 Depth
  taxonomy_8_first_letter: '1'
  taxonomy_8_first_letter_upper: '1'
  taxonomy_8_length_1: '1'
  taxonomy_8_length_2: '12'
  taxonomy_8_length_3: '12_'
  taxonomy_8_length_4: 12_d
  taxonomy_8_length_5: 12_de
  taxonomy_8_upper: 12_DEPTH
  taxonomy_8_upper_length_1: '1'
  taxonomy_8_upper_length_2: '12'
  taxonomy_8_upper_length_3: '12_'
  taxonomy_8_upper_length_4: 12_D
  taxonomy_8_upper_length_5: 12_DE
  taxonomy_9: inside_embedded_m3_nuts
  taxonomy_9_capital: Inside Embedded M3 Nuts
  taxonomy_9_first_letter: i
  taxonomy_9_first_letter_upper: I
  taxonomy_9_length_1: i
  taxonomy_9_length_2: in
  taxonomy_9_length_3: ins
  taxonomy_9_length_4: insi
  taxonomy_9_length_5: insid
  taxonomy_9_upper: INSIDE_EMBEDDED_M3_NUTS
  taxonomy_9_upper_length_1: I
  taxonomy_9_upper_length_2: IN
  taxonomy_9_upper_length_3: INS
  taxonomy_9_upper_length_4: INSI
  taxonomy_9_upper_length_5: INSID
  type: part
  url_chat: ''
  width: 7
  width_mm: 104
url_chat: ''
width: 7
