oomlout/oomlout_oobb_part_holder_bearing_version_5/navigation_oobb/oobb/part/plate_90_degree/bearing/606_bearing_size/3_width/3_height/12_depth/basic/working.yaml

bearing_size: '606'
bip_39_2_word_array:
- alley
- enough
bip_39_2_word_no_space: alleyenough
bip_39_2_word_space: alley enough
bip_39_2_word_underscore: alley_enough
bip_39_3_word_array:
- alley
- enough
- memory
bip_39_3_word_no_space: alleyenoughmemory
bip_39_3_word_space: alley enough memory
bip_39_3_word_underscore: alley_enough_memory
bip_39_full_array:
- alley
- enough
- memory
- typical
- chicken
- air
- seek
- history
- path
- gauge
- radio
- ignore
bip_39_full_no_space: alleyenoughmemorytypicalchickenairseekhistorypathgaugeradioignore
bip_39_full_space: alley enough memory typical chicken air seek history path gauge
  radio ignore
bip_39_full_underscore: alley_enough_memory_typical_chicken_air_seek_history_path_gauge_radio_ignore
depth: 12
directory: parts/oobb_part_plate_90_degree_bearing_606_bearing_size_3_width_3_height_12_depth_basic
extra: basic
height: 3
id: oobb_part_plate_90_degree_bearing_606_bearing_size_3_width_3_height_12_depth_basic
id_no_class: oobb_part_plate_90_degree_bearing_606_bearing_size_3_width_3_height_12_depth_basic
id_no_size: oobb_part_plate_90_degree_bearing_606_bearing_size_3_width_3_height_12_depth_basic
id_no_type: oobb_part_plate_90_degree_bearing_606_bearing_size_3_width_3_height_12_depth_basic
id_oobb: oobb_part_plate_90_degree_bearing_606_bearing_size_3_width_3_height_12_depth_basic
kwargs:
  bearing_size: '606'
  body: plate
  depth: 12
  extra: basic
  filter: ''
  height: 3
  horn_adapter: ''
  interior_hole_positions: []
  interior_radius_name: m3
  joining_tangent_clearance: 0.01
  modes:
  - 3dpr
  navigation: true
  oobb_name: bearing_plate_90_degree
  oomp_description_extra: m6_shaft_basic_extra_12_depth
  oomp_description_main: bearing_plate_90_degree_3_width_3_height
  oomp_mode: project
  oomp_run: true
  overwrite: true
  prepare_print: true
  print_gap: 10
  shaft: m6
  split: true
  split_z: 0
  typ: all
  type: default_bearing_plate_90_degree
  width: 3
legacy_id: oobb_bearing_plate_jack_basic_03_03_12_606
legacy_source: C:/gh/oomlout_oobb_version_3/things/oobb_bearing_plate_jack_basic_03_03_12_606
link_github: https://github.com/oomlout/oomlout_oomp_version_1_messy/tree/main/parts/oobb_part_plate_90_degree_bearing_606_bearing_size_3_width_3_height_12_depth_basic
link_main: https://github.com/oomlout/oomlout_oomp_version_1_messy/tree/main/parts/oobb_part_plate_90_degree_bearing_606_bearing_size_3_width_3_height_12_depth_basic
link_redirect: https://github.com/oomlout/oomlout_oomp_version_1_messy/tree/main/parts/oobb_part_plate_90_degree_bearing_606_bearing_size_3_width_3_height_12_depth_basic
md5: 06895e2bf5f27a0af0c361a0ec12c338
md5_10: 06895e2bf5
md5_10_upper: 06895E2BF5
md5_5: 06895
md5_5_upper: 06895
md5_6: 06895e
md5_6_alpha: 96ji
md5_6_alpha_upper: 96JI
md5_6_upper: 06895E
name: Oobb Part Plate 90 Degree Bearing 606 Bearing Size 3 Width 3 Height 12 Depth
  Basic
name_no_class: Oobb Part Plate 90 Degree Bearing 606 Bearing Size 3 Width 3 Height
  12 Depth Basic
name_no_size: Oobb Part Plate 90 Degree Bearing 606 Bearing Size 3 Width 3 Height
  12 Depth Basic
name_no_type: Oobb Part Plate 90 Degree Bearing 606 Bearing Size 3 Width 3 Height
  12 Depth Basic
name_proper: Oobb Part Plate 90 Degree Bearing 606 Bearing Size 3 Width 3 Height 12
  Depth Basic
name_space: oobb part plate 90 degree bearing 606 bearing size 3 width 3 height 12
  depth basic
name_upper: OOBB PART PLATE 90 DEGREE BEARING 606 BEARING SIZE 3 WIDTH 3 HEIGHT 12
  DEPTH BASIC
oobb_details:
  bearing_size: '606'
  body: plate
  depth: 12
  extra: basic
  height: 3
  horn_adapter: ''
  interior_hole_positions: []
  interior_radius_name: m3
  joining_tangent_clearance: 0.01
  oobb_name: bearing_plate_90_degree
  prepare_print: true
  print_gap: 10
  shaft: m6
  split: true
  split_z: 0
  width: 3
oobb_name: bearing_plate_90_degree
oomlout_ai_roboclick_1:
  actions:
  - command: text_jinja_template
    convert_to_pdf: false
    convert_to_png: false
    dict_data:
      bearing_size: '606'
      depth: 12
      directory: parts\oobb_part_plate_90_degree_bearing_606_bearing_size_3_width_3_height_12_depth_basic
      extra: basic
      height: 3
      id: oobb_part_plate_90_degree_bearing_606_bearing_size_3_width_3_height_12_depth_basic
      legacy_id: oobb_bearing_plate_jack_basic_03_03_12_606
      legacy_source: C:/gh/oomlout_oobb_version_3/things/oobb_bearing_plate_jack_basic_03_03_12_606
      name: oobb_part_plate_90_degree_bearing_606_bearing_size_3_width_3_height_12_depth_basic
      name_proper: Oobb Part Plate 90 Degree Bearing 606 Bearing Size 3 Width 3 Height
        12 Depth Basic
      name_space: oobb part plate 90 degree bearing 606 bearing size 3 width 3 height
        12 depth basic
      name_upper: OOBB PART PLATE 90 DEGREE BEARING 606 BEARING SIZE 3 WIDTH 3 HEIGHT
        12 DEPTH BASIC
      oobb_details:
        bearing_size: '606'
        body: plate
        depth: 12
        extra: basic
        height: 3
        horn_adapter: ''
        interior_hole_positions: []
        interior_radius_name: m3
        joining_tangent_clearance: 0.01
        oobb_name: bearing_plate_90_degree
        prepare_print: true
        print_gap: 10
        shaft: m6
        split: true
        split_z: 0
        width: 3
      plate_type: plate_90_degree
      taxonomy_1: oobb
      taxonomy_10: ''
      taxonomy_11: ''
      taxonomy_12: ''
      taxonomy_13: ''
      taxonomy_14: ''
      taxonomy_15: ''
      taxonomy_2: part
      taxonomy_3: plate_90_degree
      taxonomy_4: bearing
      taxonomy_5: 606_bearing_size
      taxonomy_6: 3_width
      taxonomy_7: 3_height
      taxonomy_8: 12_depth
      taxonomy_9: basic
      url_chat: ''
      width: 3
    dict_data_files: {}
    dict_data_files_exists: {}
    file_output: label_oomp.svg
    file_template: C:\gh\oomlout_oobb_part_plate_bearing_version_5\source_file\template_jinja\template_jinja_label_oomlout_76_2_mm_50_8_mm\working.svg.j2
    search_and_replace: []
  file_test: label_oomp.pdf
  retries_until_complete: 0
oomp_key: oomp_oobb_part_plate_90_degree_bearing_606_bearing_size_3_width_3_height_12_depth_basic
plate_type: plate_90_degree
project_name: C:\gh\oomlout_oobb_part_plate_bearing_version_5
taxonomy_1: oobb
taxonomy_10: ''
taxonomy_11: ''
taxonomy_12: ''
taxonomy_13: ''
taxonomy_14: ''
taxonomy_15: ''
taxonomy_1_capital: Oobb
taxonomy_1_first_letter: o
taxonomy_1_first_letter_upper: O
taxonomy_1_length_1: o
taxonomy_1_length_2: oo
taxonomy_1_length_3: oob
taxonomy_1_length_4: oobb
taxonomy_1_length_5: oobb
taxonomy_1_upper: OOBB
taxonomy_1_upper_length_1: O
taxonomy_1_upper_length_2: OO
taxonomy_1_upper_length_3: OOB
taxonomy_1_upper_length_4: OOBB
taxonomy_1_upper_length_5: OOBB
taxonomy_2: part
taxonomy_2_capital: Part
taxonomy_2_first_letter: p
taxonomy_2_first_letter_upper: P
taxonomy_2_length_1: p
taxonomy_2_length_2: pa
taxonomy_2_length_3: par
taxonomy_2_length_4: part
taxonomy_2_length_5: part
taxonomy_2_upper: PART
taxonomy_2_upper_length_1: P
taxonomy_2_upper_length_2: PA
taxonomy_2_upper_length_3: PAR
taxonomy_2_upper_length_4: PART
taxonomy_2_upper_length_5: PART
taxonomy_3: plate_90_degree
taxonomy_3_capital: Plate 90 Degree
taxonomy_3_first_letter: p
taxonomy_3_first_letter_upper: P
taxonomy_3_length_1: p
taxonomy_3_length_2: pl
taxonomy_3_length_3: pla
taxonomy_3_length_4: plat
taxonomy_3_length_5: plate
taxonomy_3_upper: PLATE_90_DEGREE
taxonomy_3_upper_length_1: P
taxonomy_3_upper_length_2: PL
taxonomy_3_upper_length_3: PLA
taxonomy_3_upper_length_4: PLAT
taxonomy_3_upper_length_5: PLATE
taxonomy_4: bearing
taxonomy_4_capital: Bearing
taxonomy_4_first_letter: b
taxonomy_4_first_letter_upper: B
taxonomy_4_length_1: b
taxonomy_4_length_2: be
taxonomy_4_length_3: bea
taxonomy_4_length_4: bear
taxonomy_4_length_5: beari
taxonomy_4_upper: BEARING
taxonomy_4_upper_length_1: B
taxonomy_4_upper_length_2: BE
taxonomy_4_upper_length_3: BEA
taxonomy_4_upper_length_4: BEAR
taxonomy_4_upper_length_5: BEARI
taxonomy_5: 606_bearing_size
taxonomy_5_capital: 606 Bearing Size
taxonomy_5_first_letter: '6'
taxonomy_5_first_letter_upper: '6'
taxonomy_5_length_1: '6'
taxonomy_5_length_2: '60'
taxonomy_5_length_3: '606'
taxonomy_5_length_4: '606_'
taxonomy_5_length_5: 606_b
taxonomy_5_upper: 606_BEARING_SIZE
taxonomy_5_upper_length_1: '6'
taxonomy_5_upper_length_2: '60'
taxonomy_5_upper_length_3: '606'
taxonomy_5_upper_length_4: '606_'
taxonomy_5_upper_length_5: 606_B
taxonomy_6: 3_width
taxonomy_6_capital: 3 Width
taxonomy_6_first_letter: '3'
taxonomy_6_first_letter_upper: '3'
taxonomy_6_length_1: '3'
taxonomy_6_length_2: '3_'
taxonomy_6_length_3: 3_w
taxonomy_6_length_4: 3_wi
taxonomy_6_length_5: 3_wid
taxonomy_6_upper: 3_WIDTH
taxonomy_6_upper_length_1: '3'
taxonomy_6_upper_length_2: '3_'
taxonomy_6_upper_length_3: 3_W
taxonomy_6_upper_length_4: 3_WI
taxonomy_6_upper_length_5: 3_WID
taxonomy_7: 3_height
taxonomy_7_capital: 3 Height
taxonomy_7_first_letter: '3'
taxonomy_7_first_letter_upper: '3'
taxonomy_7_length_1: '3'
taxonomy_7_length_2: '3_'
taxonomy_7_length_3: 3_h
taxonomy_7_length_4: 3_he
taxonomy_7_length_5: 3_hei
taxonomy_7_upper: 3_HEIGHT
taxonomy_7_upper_length_1: '3'
taxonomy_7_upper_length_2: '3_'
taxonomy_7_upper_length_3: 3_H
taxonomy_7_upper_length_4: 3_HE
taxonomy_7_upper_length_5: 3_HEI
taxonomy_8: 12_depth
taxonomy_8_capital: 12 Depth
taxonomy_8_first_letter: '1'
taxonomy_8_first_letter_upper: '1'
taxonomy_8_length_1: '1'
taxonomy_8_length_2: '12'
taxonomy_8_length_3: '12_'
taxonomy_8_length_4: 12_d
taxonomy_8_length_5: 12_de
taxonomy_8_upper: 12_DEPTH
taxonomy_8_upper_length_1: '1'
taxonomy_8_upper_length_2: '12'
taxonomy_8_upper_length_3: '12_'
taxonomy_8_upper_length_4: 12_D
taxonomy_8_upper_length_5: 12_DE
taxonomy_9: basic
taxonomy_9_capital: Basic
taxonomy_9_first_letter: b
taxonomy_9_first_letter_upper: B
taxonomy_9_length_1: b
taxonomy_9_length_2: ba
taxonomy_9_length_3: bas
taxonomy_9_length_4: basi
taxonomy_9_length_5: basic
taxonomy_9_upper: BASIC
taxonomy_9_upper_length_1: B
taxonomy_9_upper_length_2: BA
taxonomy_9_upper_length_3: BAS
taxonomy_9_upper_length_4: BASI
taxonomy_9_upper_length_5: BASIC
url_chat: ''
width: 3
