oomlout/oomlout_oobb_part_holder_bearing_version_5/parts_source/oobb_part_plate_bearing_608_bearing_size_3_width_3_height_12_depth/working.yaml

bearing_depth: 7
bearing_dimension_source: https://www.emarketplace.in.skf.com/industrial/bearings?search=608-RSH
bearing_inner_diameter: 8
bearing_outer_diameter: 22
bearing_print_radial_clearance: 0.2
bearing_size: '608'
depth: 12
extra: ''
height: 3
id: oobb_part_plate_bearing_608_bearing_size_3_width_3_height_12_depth
interior_grid: 0
oobb_details:
  bearing_depth: 7
  bearing_inner_diameter: 8
  bearing_outer_diameter: 22
  bearing_print_radial_clearance: 0.2
  bearing_size: '608'
  body: plate
  depth: 12
  extra: ''
  height: 3
  horn_adapter: ''
  interior_grid: 0
  interior_hole_positions: []
  interior_radius_name: m3
  joining_tangent_clearance: 0.01
  oobb_name: bearing_plate
  prepare_print: true
  print_gap: 10
  shaft: m6
  split: true
  split_z: 0
  width: 3
taxonomy_1: oobb
taxonomy_10: ''
taxonomy_11: ''
taxonomy_12: ''
taxonomy_13: ''
taxonomy_14: ''
taxonomy_15: ''
taxonomy_2: part
taxonomy_3: plate
taxonomy_4: bearing
taxonomy_5: 608_bearing_size
taxonomy_6: 3_width
taxonomy_7: 3_height
taxonomy_8: 12_depth
taxonomy_9: ''
width: 3
