oomlout/oomlout_oobb_part_holder_bearing_version_5/parts_source/oobb_part_plate_bearing_6705_bearing_size_3_width_3_height_12_depth_inside_embedded_m3_nuts/working.yaml

bearing_size: '6705'
depth: 12
embedded_nut_positions: &id001
- - -7.5
  - 0
- - 7.5
  - 0
- - 0
  - -7.5
- - 0
  - 7.5
embedded_nut_rotation: 30
embedded_nut_rotation_radial: true
extra: inside_embedded_m3_nuts
height: 3
id: oobb_part_plate_bearing_6705_bearing_size_3_width_3_height_12_depth_inside_embedded_m3_nuts
inner_joining_rotation: 45
inside: embedded_m3_nuts
oobb_details:
  bearing_size: '6705'
  body: plate
  depth: 12
  embedded_nut_positions: *id001
  embedded_nut_rotation: 30
  embedded_nut_rotation_radial: true
  extra: inside_embedded_m3_nuts
  height: 3
  horn_adapter: ''
  inner_joining_rotation: 45
  inside: embedded_m3_nuts
  interior_hole_positions: []
  interior_radius_name: m3
  joining_tangent_clearance: 0.01
  oobb_name: bearing_plate
  prepare_print: true
  print_gap: 10
  shaft: m6
  split: true
  split_z: 0
  width: 3
taxonomy_1: oobb
taxonomy_10: ''
taxonomy_11: ''
taxonomy_12: ''
taxonomy_13: ''
taxonomy_14: ''
taxonomy_15: ''
taxonomy_2: part
taxonomy_3: plate
taxonomy_4: bearing
taxonomy_5: 6705_bearing_size
taxonomy_6: 3_width
taxonomy_7: 3_height
taxonomy_8: 12_depth
taxonomy_9: inside_embedded_m3_nuts
width: 3
