oomlout/oomlout_oobb_part_holder_bearing_version_5/working_oomp_populate.py

"""Existing working.py / OOMP entry point; edit the catalogue in working_populate."""

from oomp_populate_helper import build_oomp_id
import working_populate


def main(**kwargs):
    return working_populate.main(**kwargs)


if __name__ == "__main__":
    main()
